d5aa962e/Transroc/images/Exploded_View.png

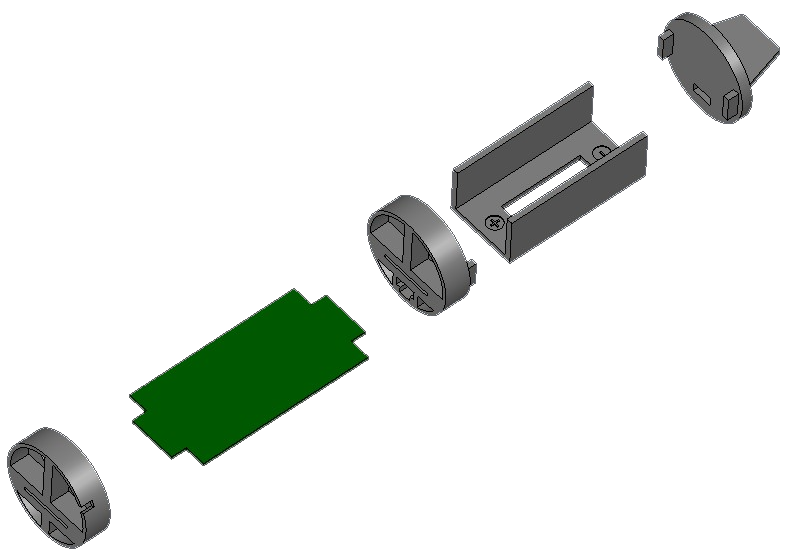
images/Exploded_View.png
