d5aa962e/Transroc/Photos/3D Model.png

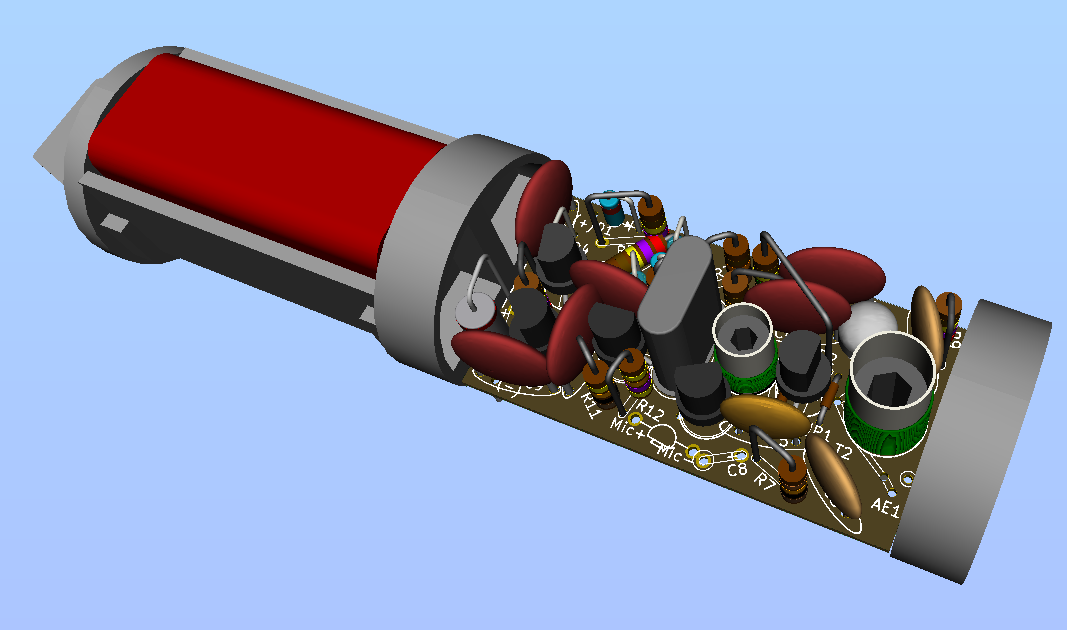
Photos/3D Model.png
