d5aa962e/Transroc/Photos/20210210_202059.jpg

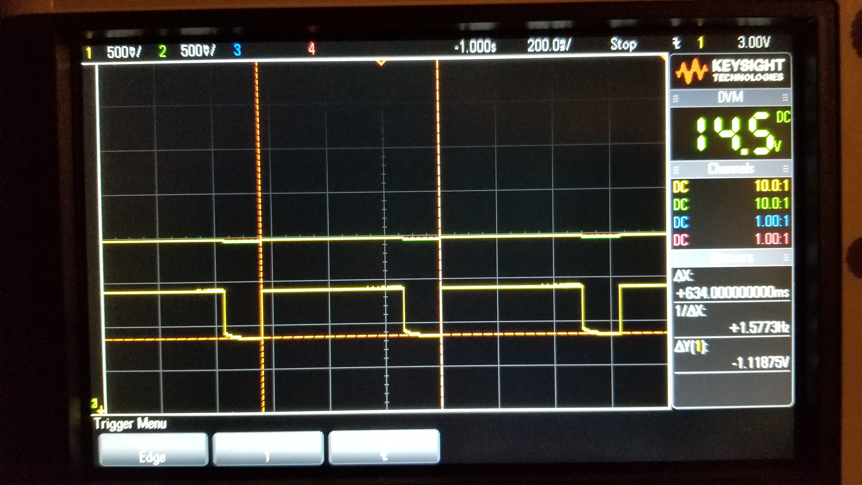
Photos/20210210_202059.jpg
