d5aa962e/Transroc/Photos/20210210_202735.jpg

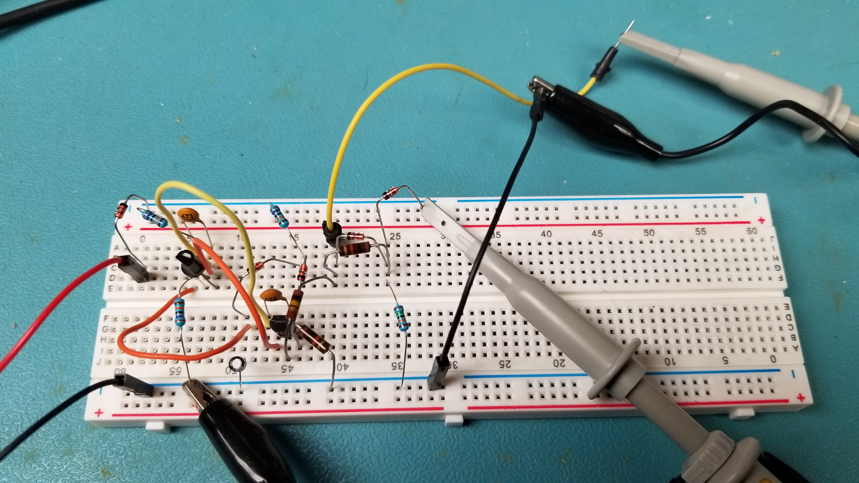
Photos/20210210_202735.jpg
