d5aa962e/Transroc/Photos/20210211_202033.jpg

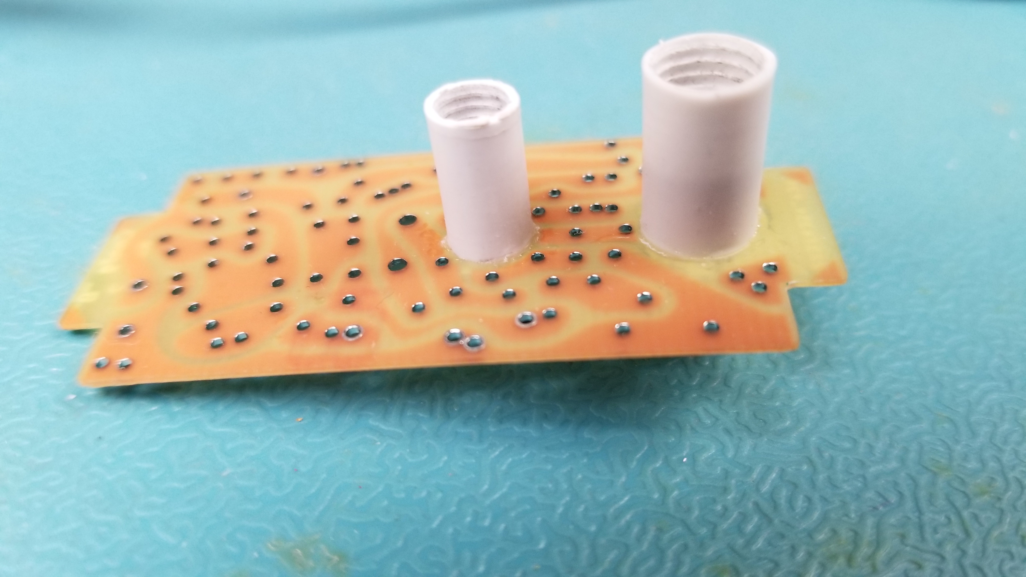
Photos/20210211_202033.jpg
