d5aa962e/Transroc/Photos/20210211_202049.jpg

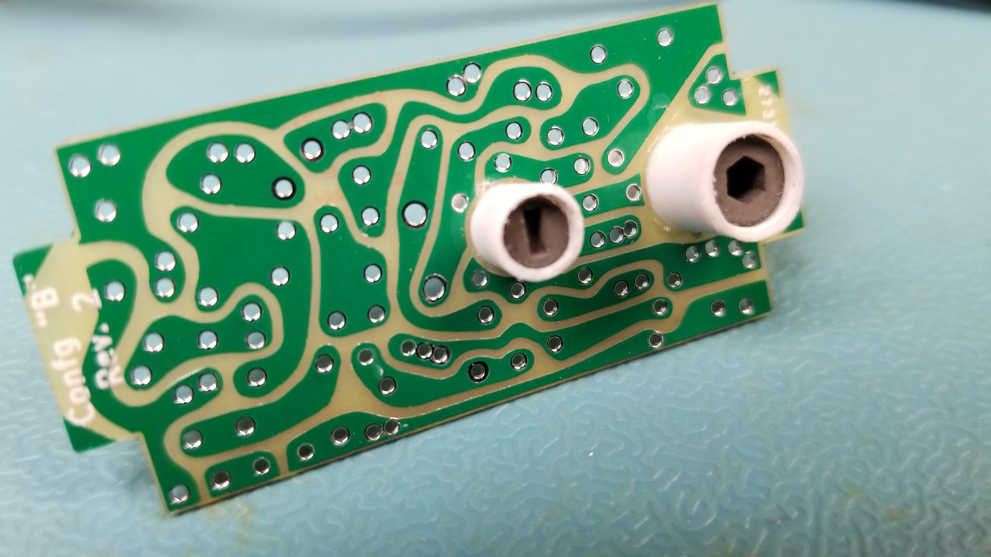
Photos/20210211_202049.jpg
