d5aa962e/Transroc/Photos/20210211_203920.jpg

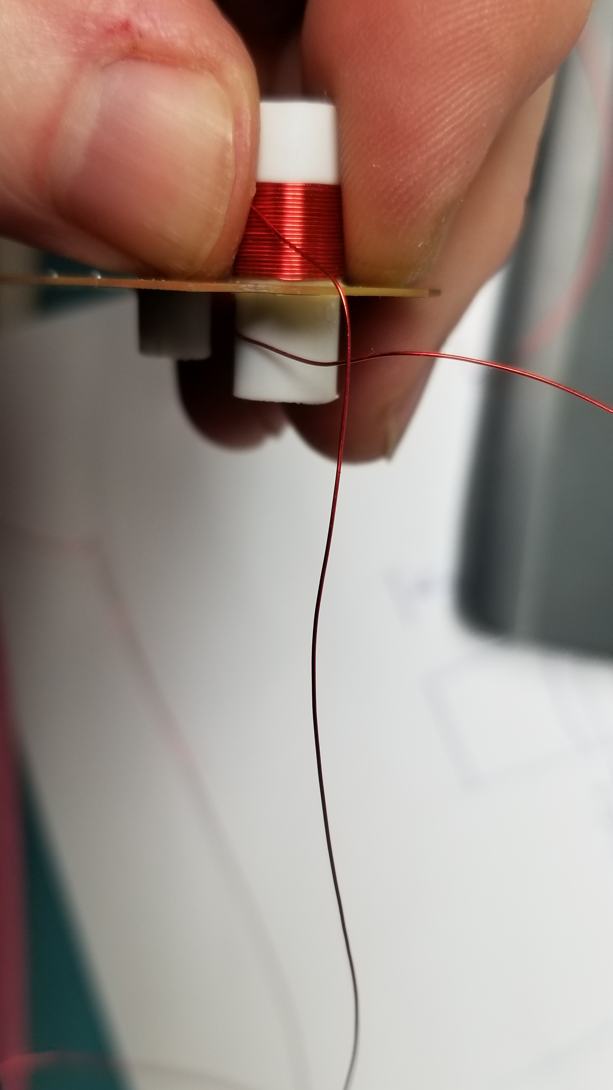
Photos/20210211_203920.jpg
