d5aa962e/Transroc/Photos/20210213_082918.jpg

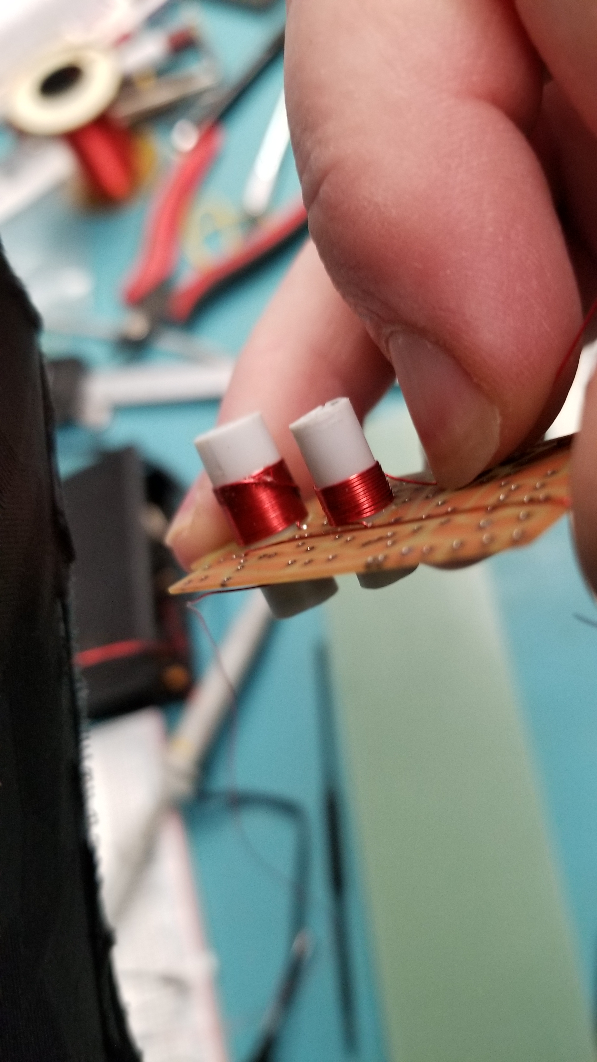
Photos/20210213_082918.jpg
