d5aa962e/Transroc/Photos/20210707_223943.jpg

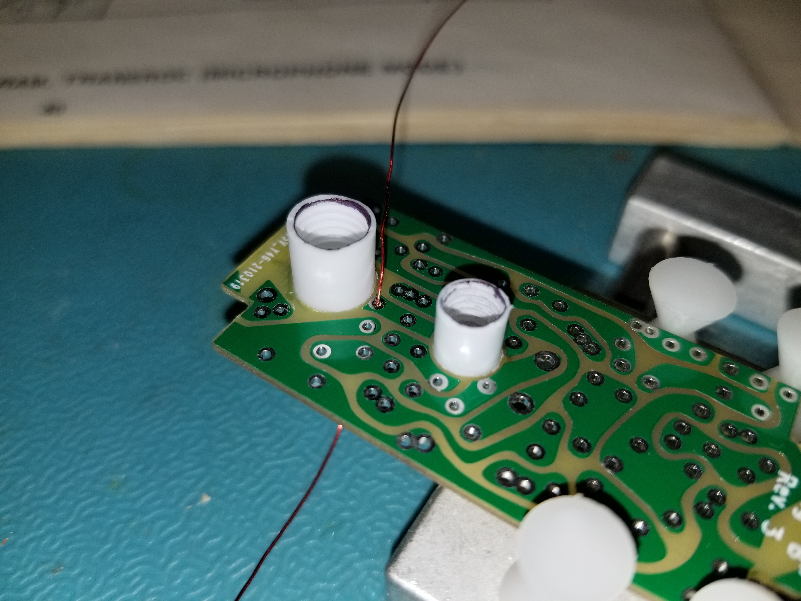
Photos/20210707_223943.jpg
