d5aa962e/Transroc/Photos/20210707_230140.jpg

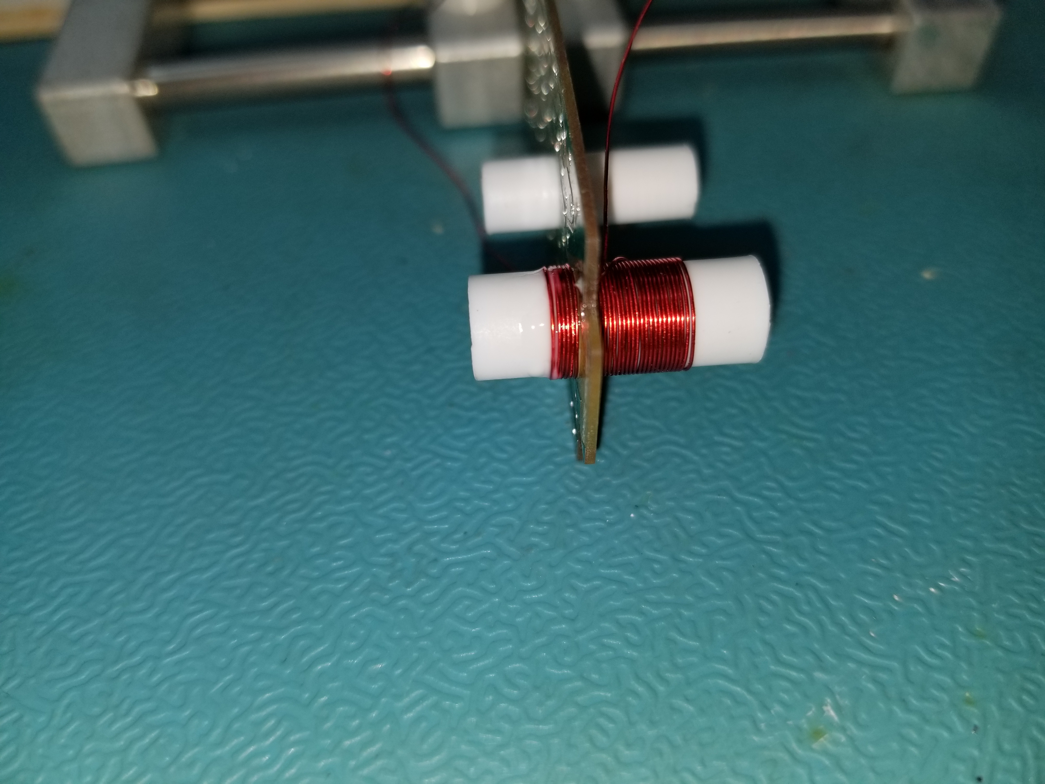
Photos/20210707_230140.jpg
