d5aa962e/Transroc/Photos/20210707_232322.jpg

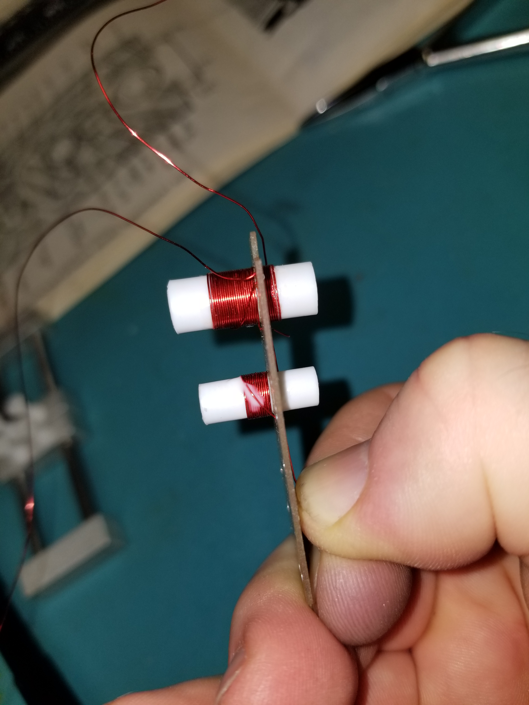
Photos/20210707_232322.jpg
