d5aa962e/Transroc/Photos/20210707_233321.jpg

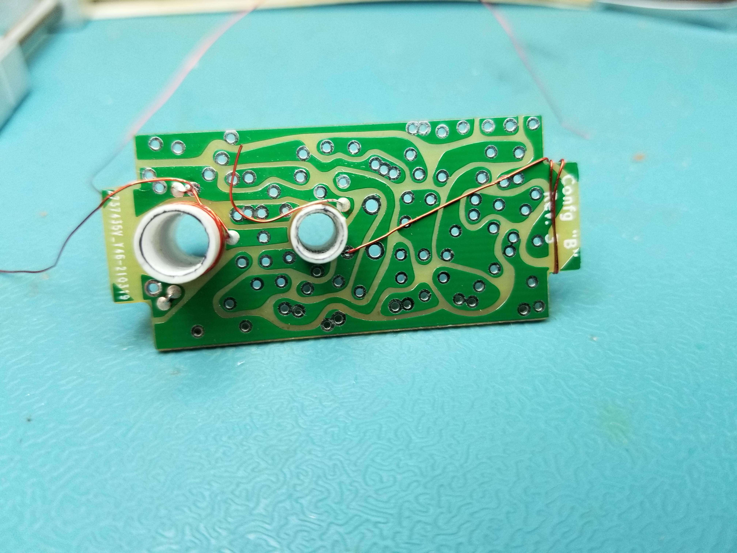
Photos/20210707_233321.jpg
