d5aa962e/Transroc/Photos/20210708_203227.jpg

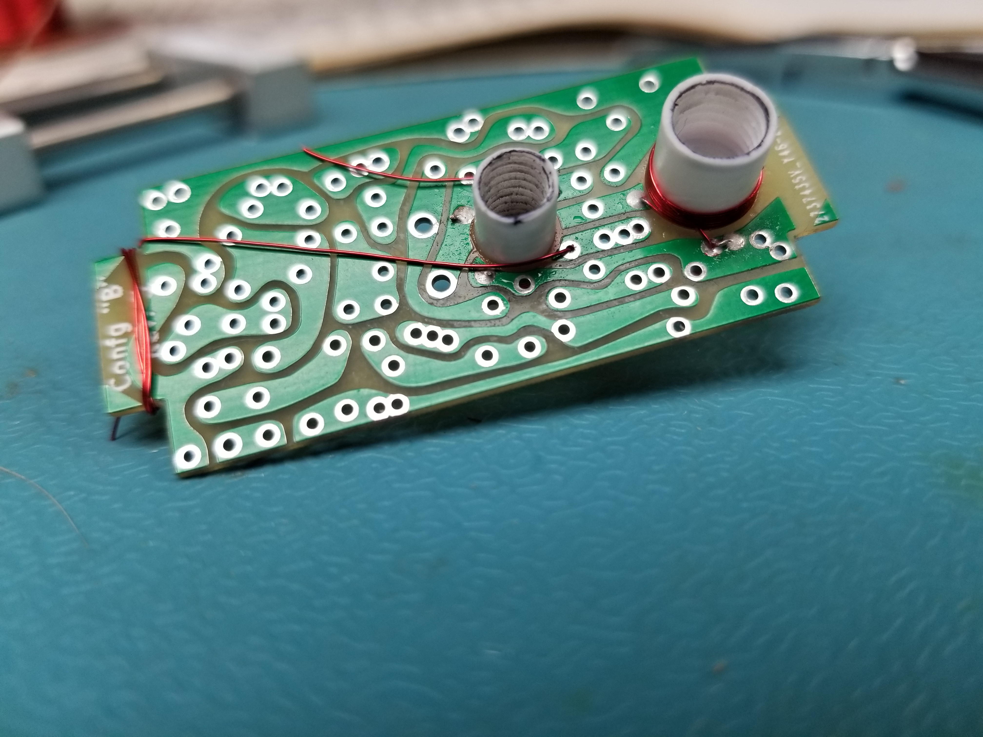
Photos/20210708_203227.jpg
