d5aa962e/Transroc/Photos/20210708_211325.jpg

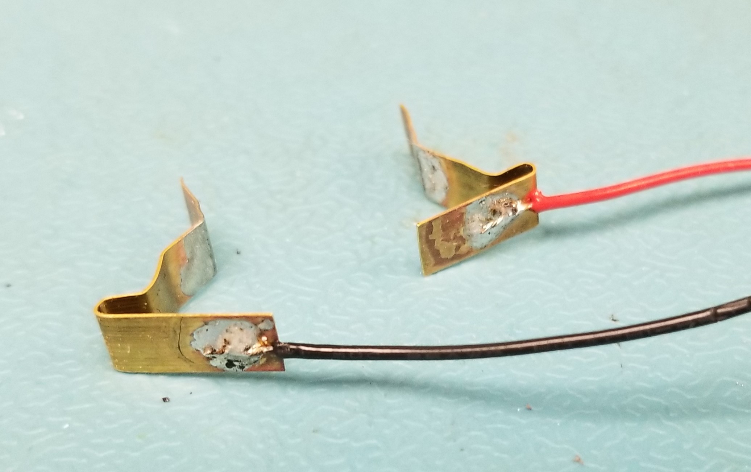
Photos/20210708_211325.jpg
