d5aa962e/Transroc/Photos/20210708_211338.jpg

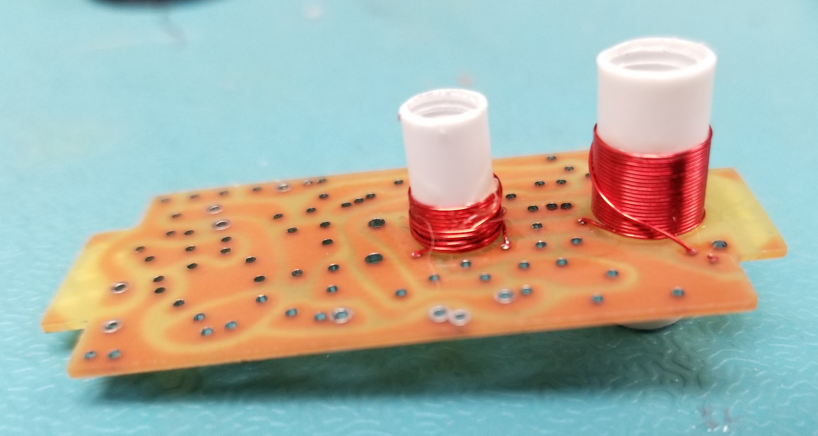
Photos/20210708_211338.jpg
