d5aa962e/Transroc/Photos/20210708_211359.jpg

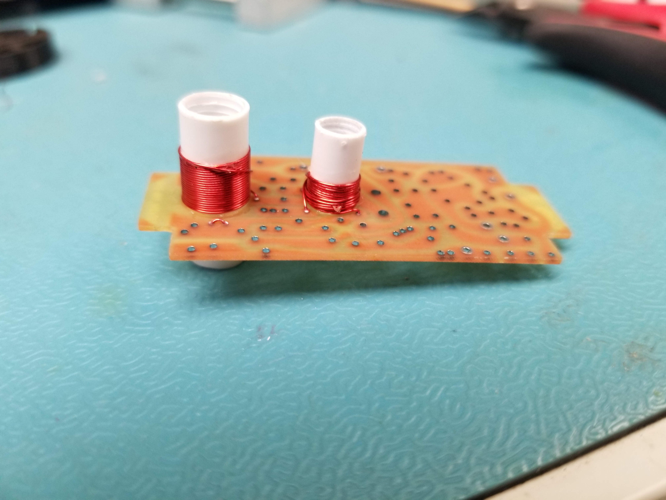
Photos/20210708_211359.jpg
