d5aa962e/Transroc/Photos/20210708_211550.jpg

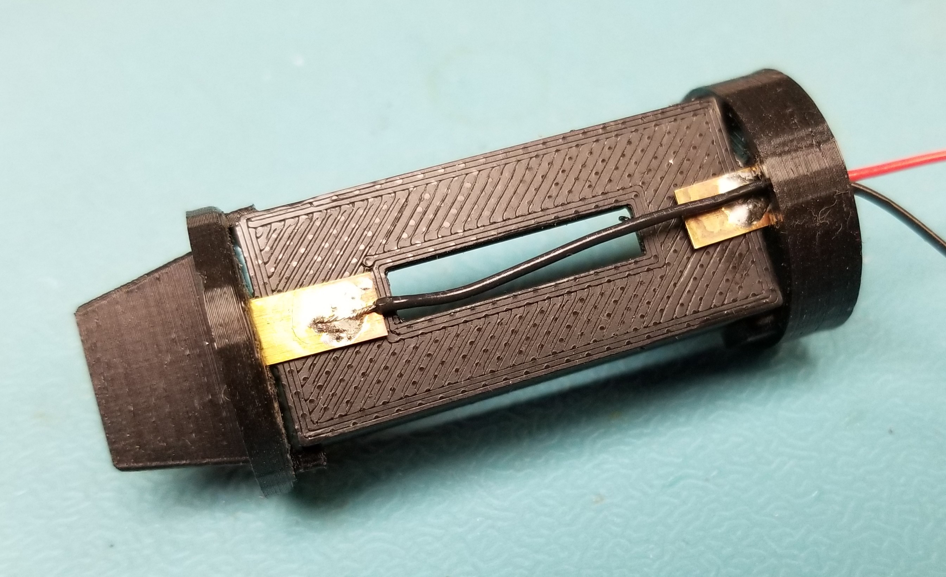
Photos/20210708_211550.jpg
