d5aa962e/Transroc/Photos/20210708_213011.jpg

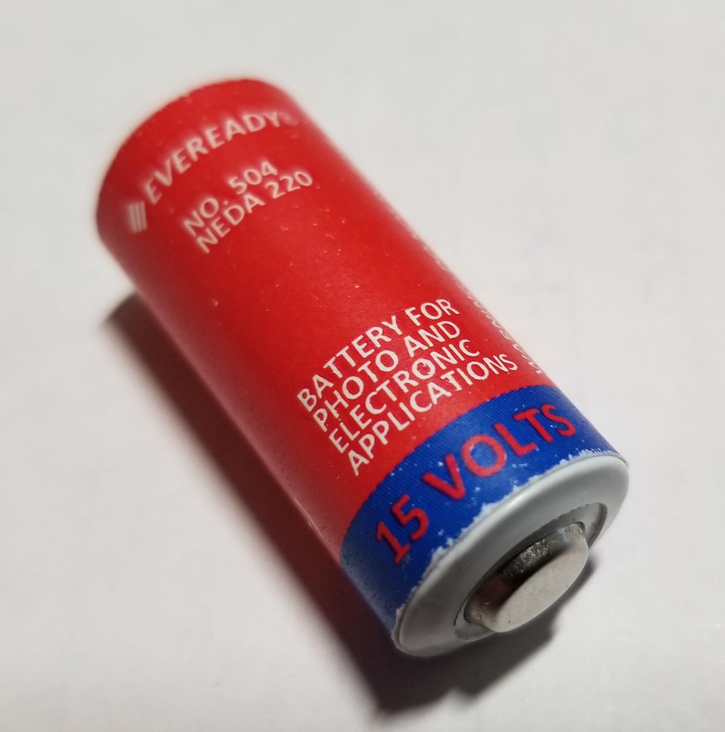
Photos/20210708_213011.jpg
