d5aa962e/Transroc/Photos/20210708_214236-a.jpg

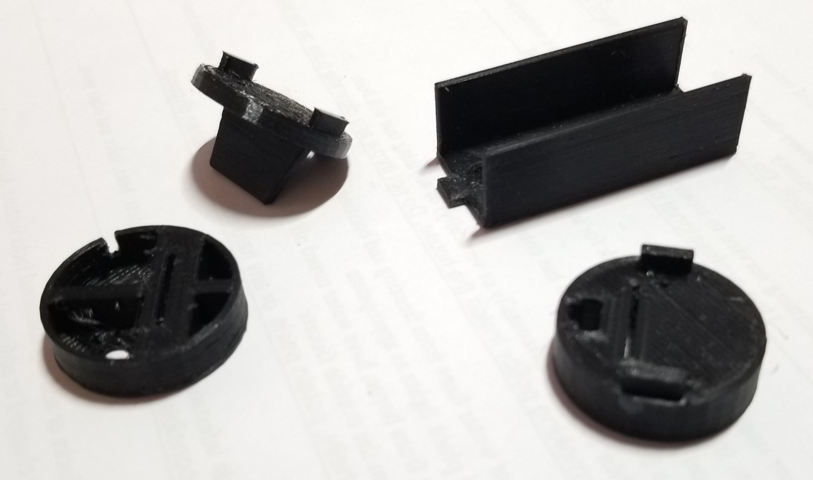
Photos/20210708_214236-a.jpg
