d5aa962e/Transroc/Photos/20210826_221735a.jpg

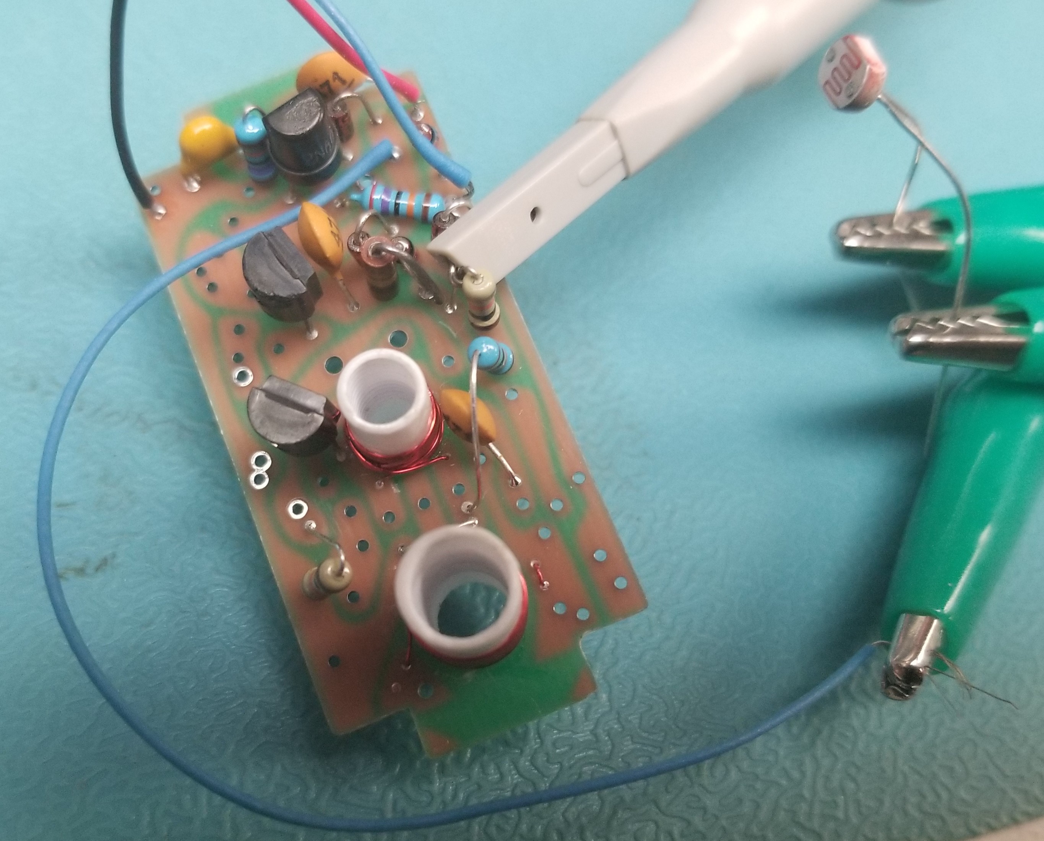
Photos/20210826_221735a.jpg
