d5aa962e/Transroc/Photos/20210826_221752.jpg

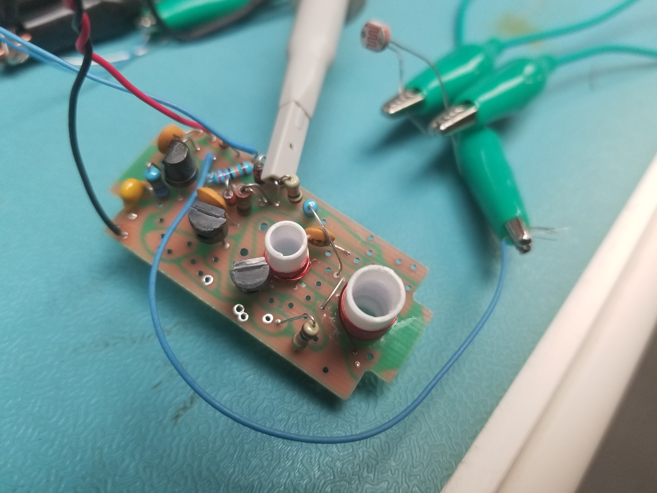
Photos/20210826_221752.jpg
