d5aa962e/Transroc/Photos/20210830_192405.jpg

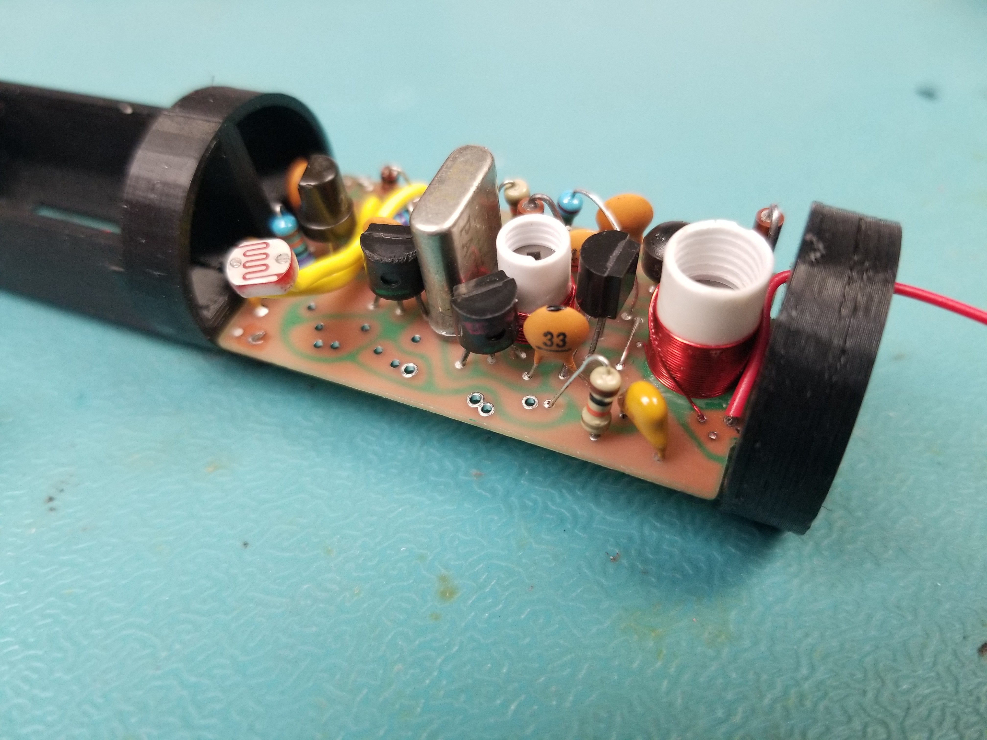
Photos/20210830_192405.jpg
