d5aa962e/Transroc/Photos/20210830_200806.jpg

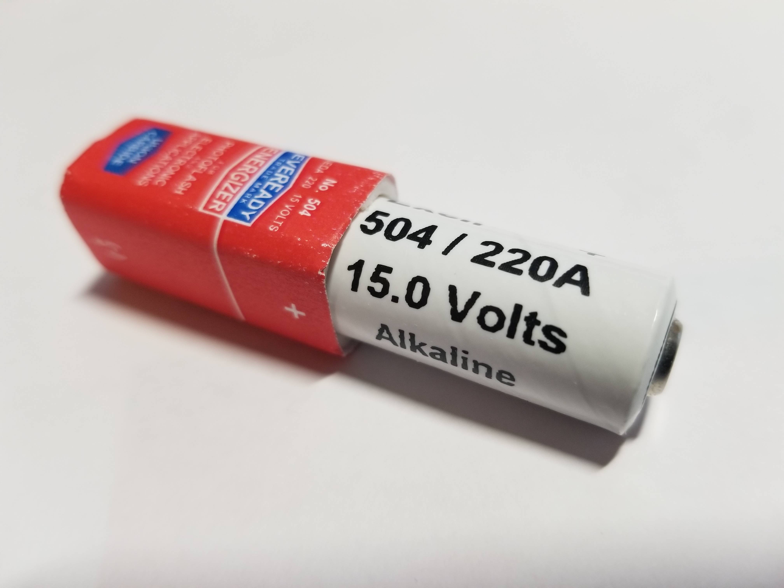
Photos/20210830_200806.jpg
