d5aa962e/Transroc/Photos/20210830_201057.jpg

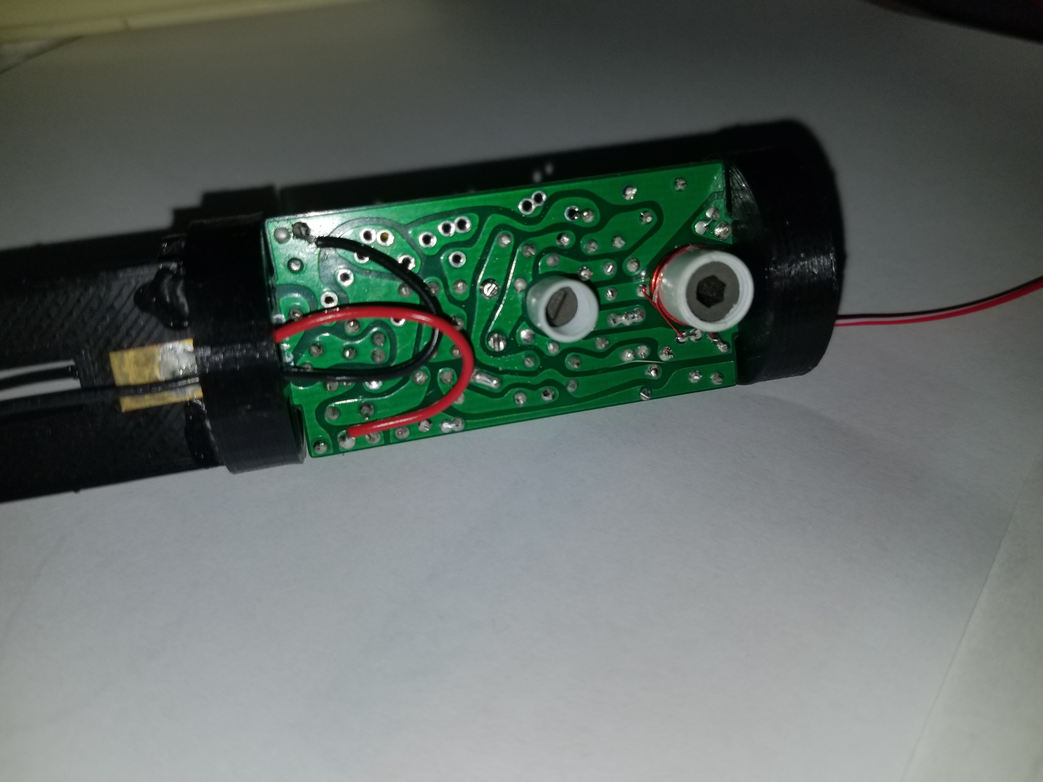
Photos/20210830_201057.jpg
