d5aa962e/Transroc/Photos/20210830_201219.jpg

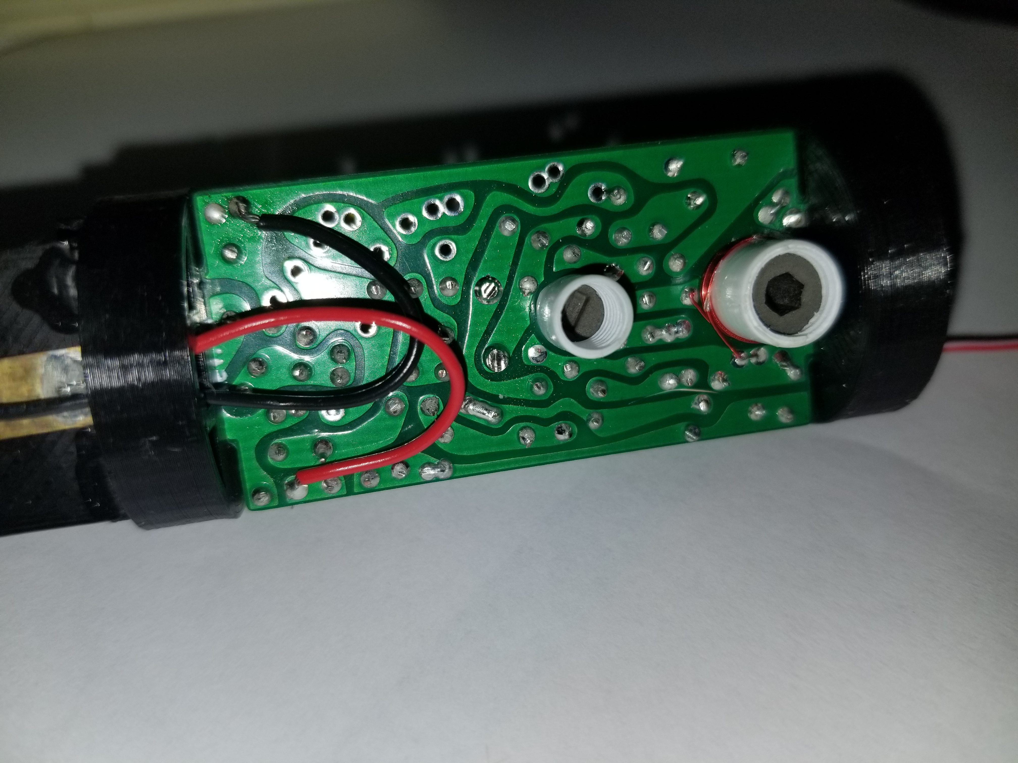
Photos/20210830_201219.jpg
