d5aa962e/Transroc/Photos/20210830_201253.jpg

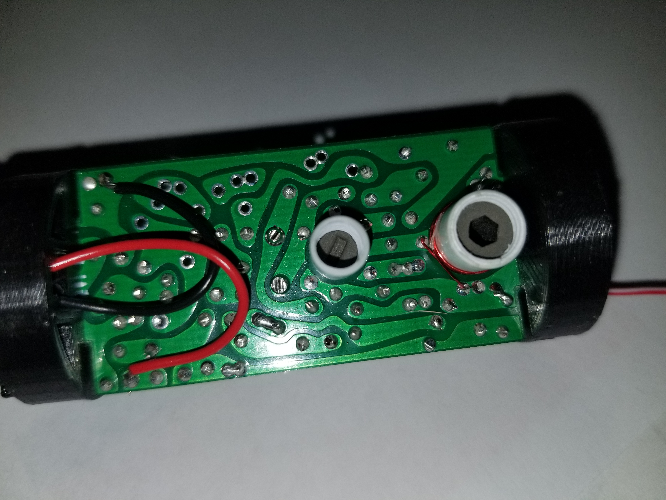
Photos/20210830_201253.jpg
