d5aa962e/Transroc/Photos/20210830_201328.jpg

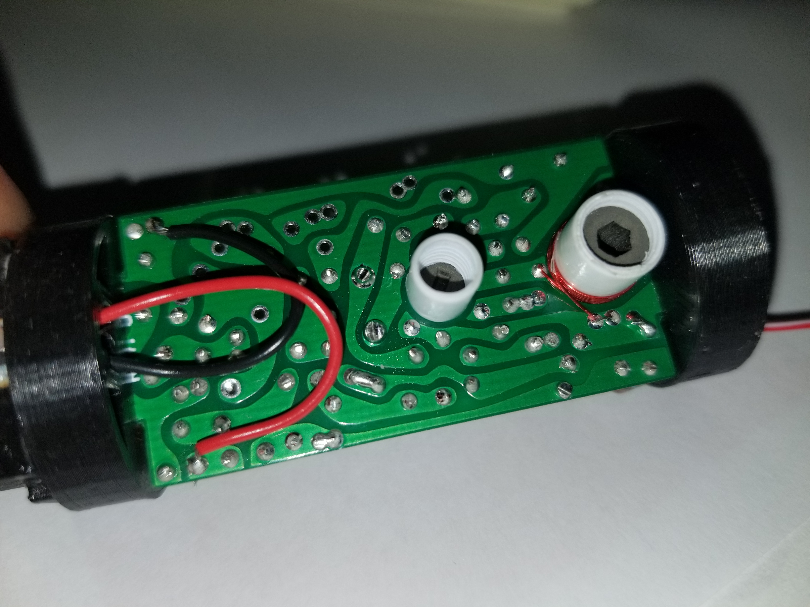
Photos/20210830_201328.jpg
