d5aa962e/Transroc/Photos/Blank Boards.jpg

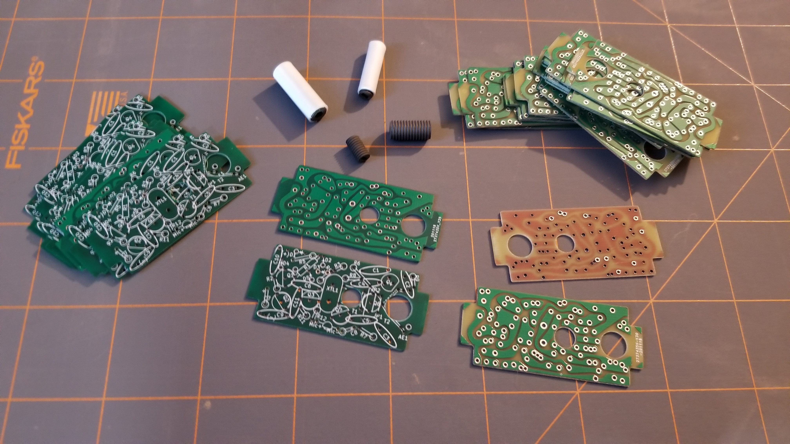
Photos/Blank Boards.jpg
