d5aa962e/Transroc/Photos/RocketGuy101_Models/P5262098MR.jpg

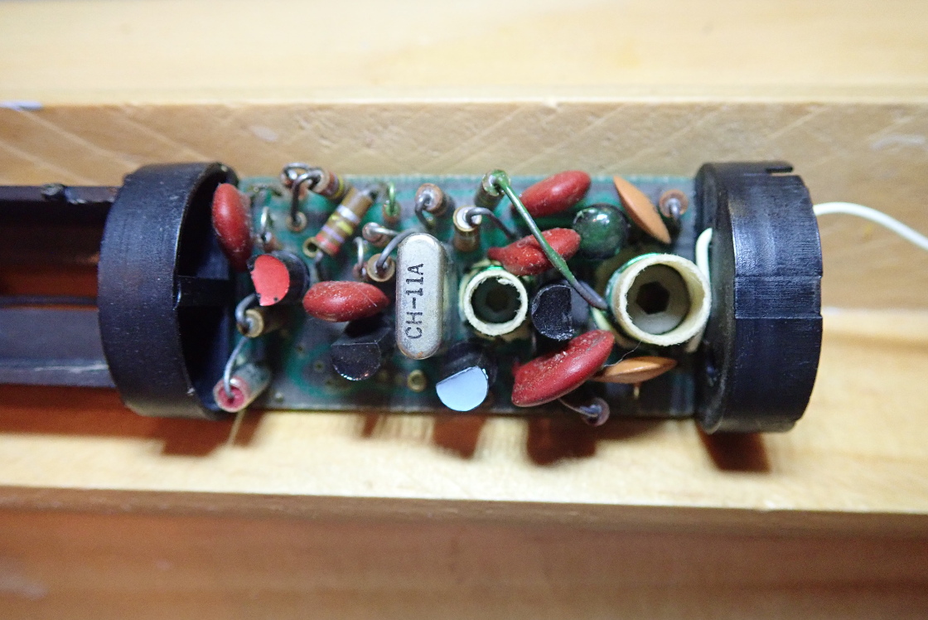
Photos/RocketGuy101_Models/P5262098MR.jpg
