d5aa962e/Transroc/Photos/RocketGuy101_Models/P6262291.jpg

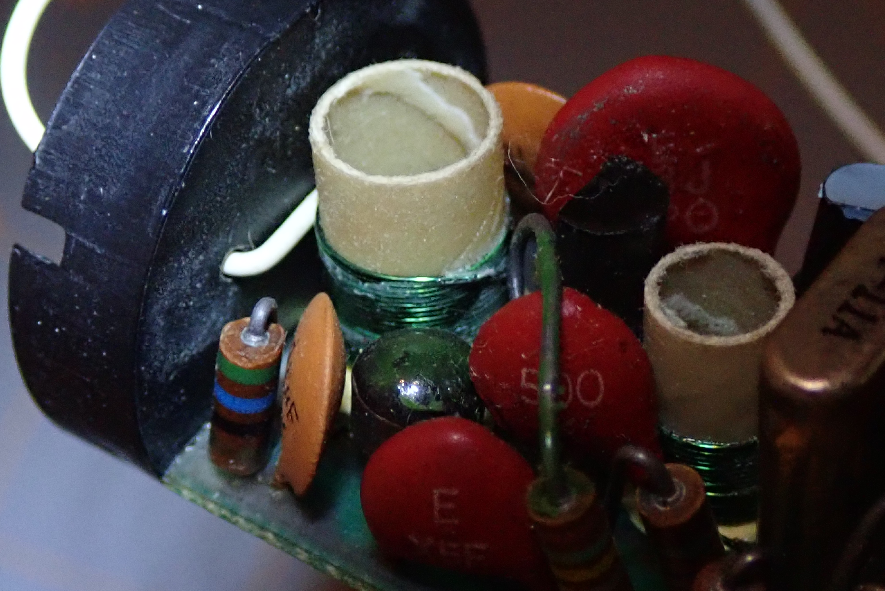
Photos/RocketGuy101_Models/P6262291.jpg
