d5aa962e/Transroc/Photos/RocketGuy101_Models/P6262298.jpg

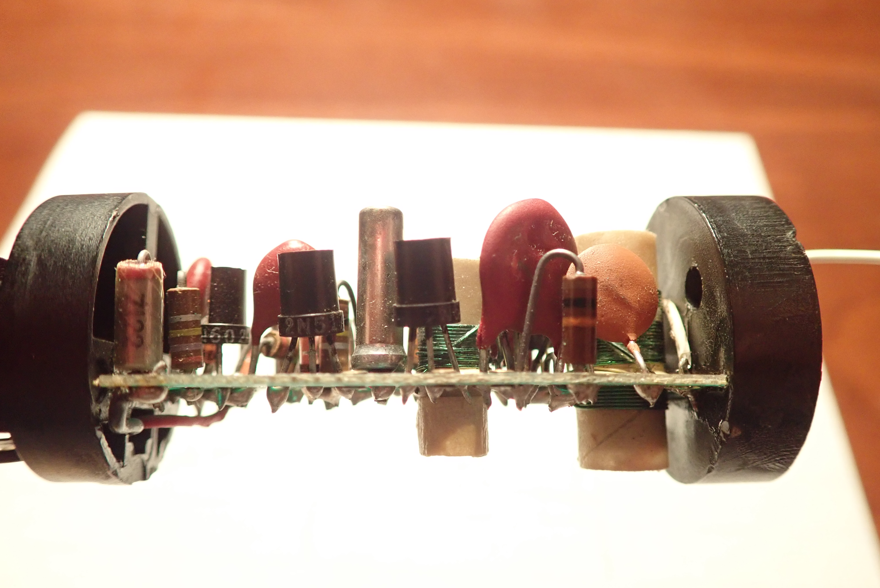
Photos/RocketGuy101_Models/P6262298.jpg
