d5aa962e/Transroc/Photos/RocketGuy101_Models/P6262299.jpg

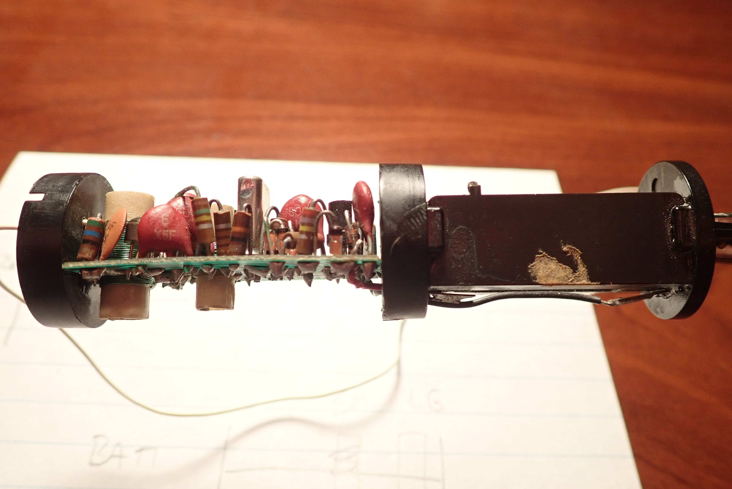
Photos/RocketGuy101_Models/P6262299.jpg
