d5aa962e/Transroc/Photos/RocketGuy101_Models/P6262300.jpg

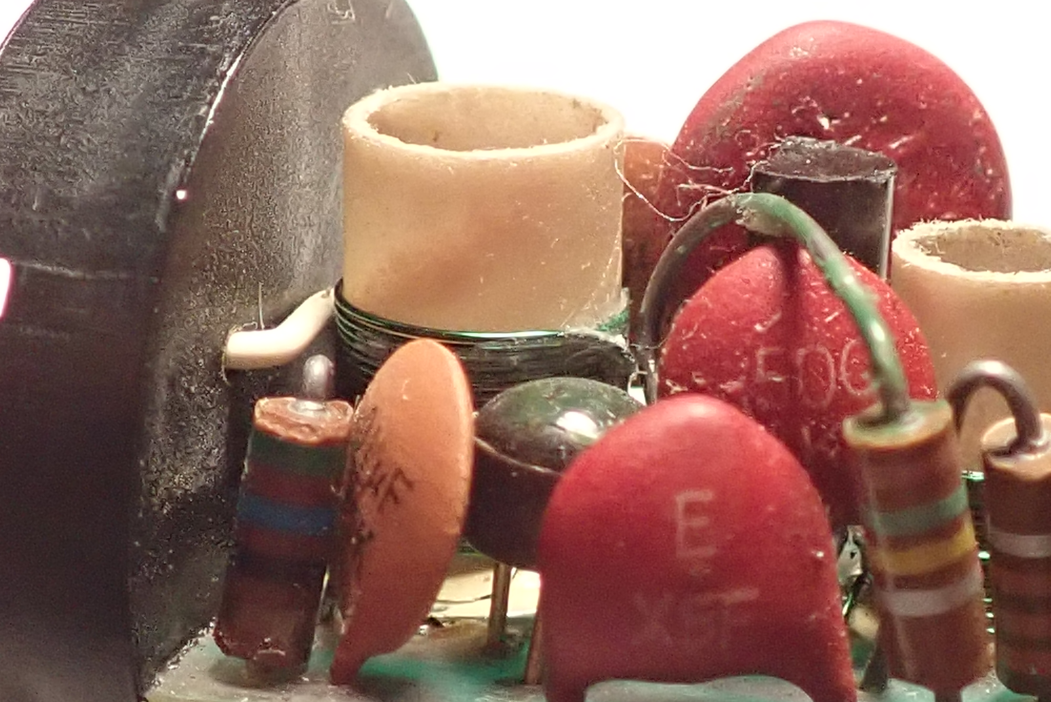
Photos/RocketGuy101_Models/P6262300.jpg
