d5aa962e/Transroc/Photos/RocketGuy101_Models/P6262301.jpg

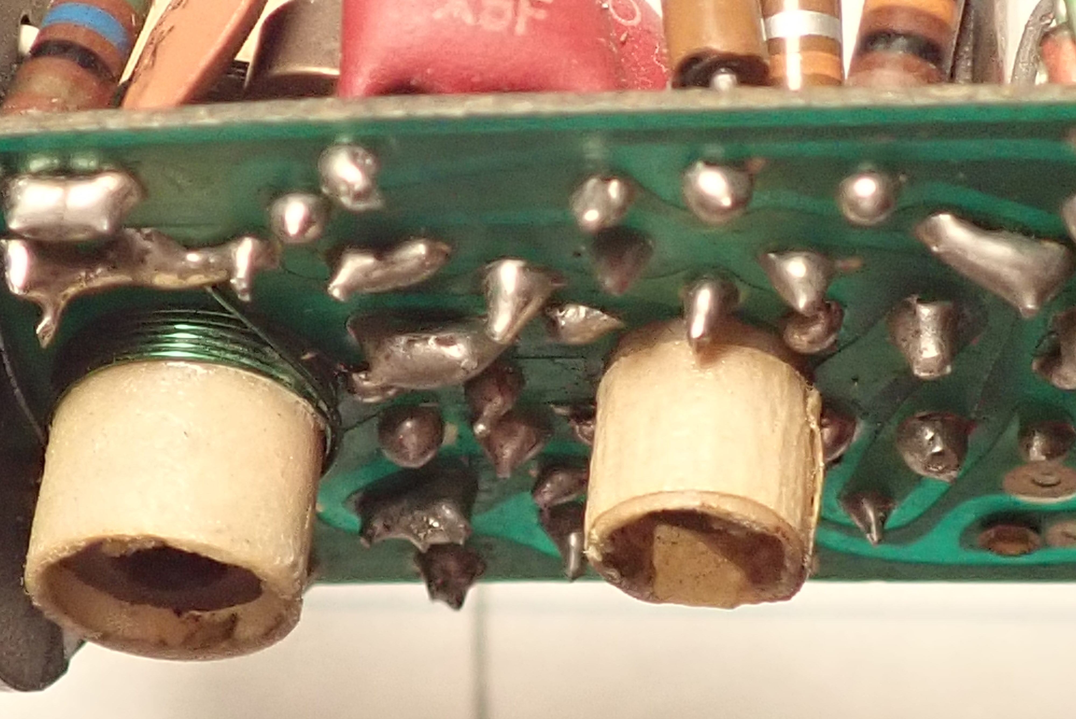
Photos/RocketGuy101_Models/P6262301.jpg
