d5aa962e/Transroc/Photos/RocketGuy101_Models/TransrocAssy.jpg

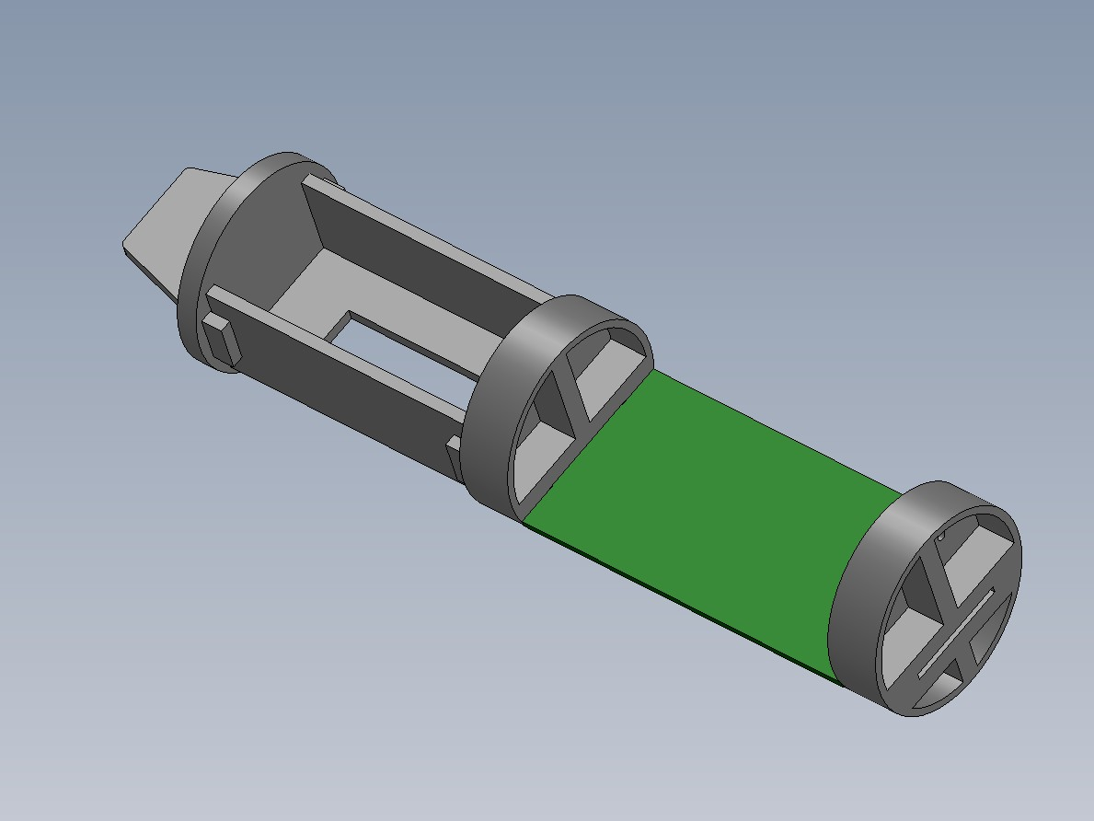
Photos/RocketGuy101_Models/TransrocAssy.jpg
