d5aa962e/Transroc/Photos/RocketGuy101_Models/TransrocAssyExp.jpg

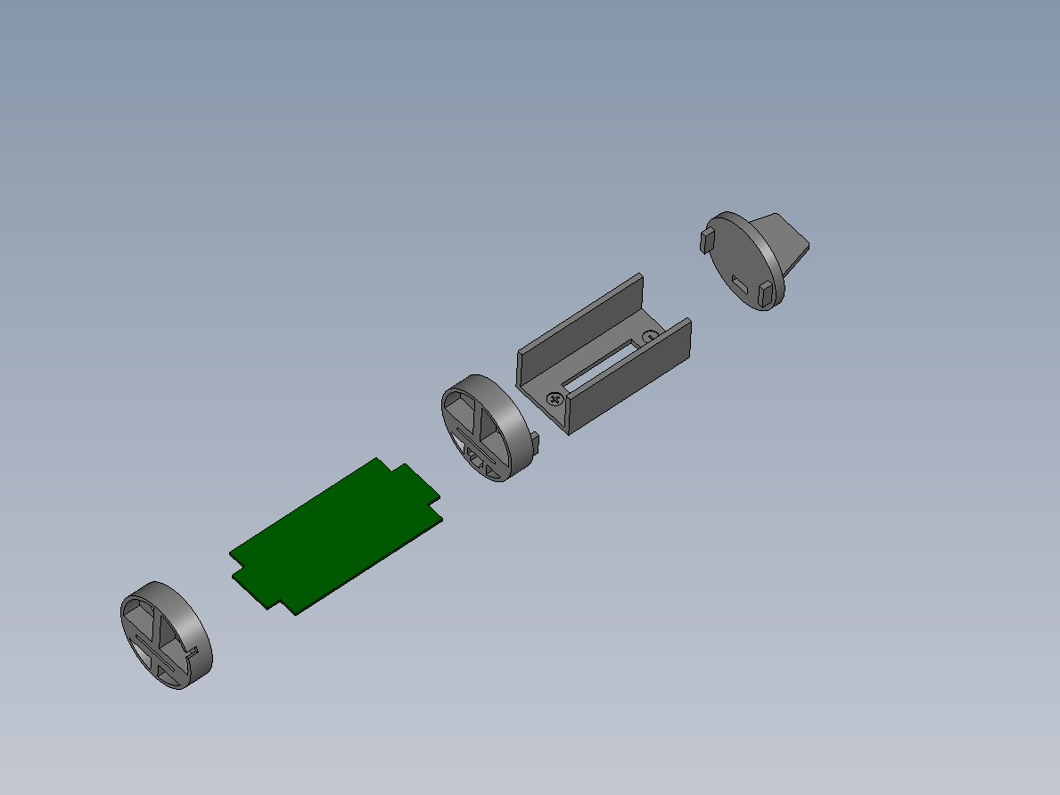
Photos/RocketGuy101_Models/TransrocAssyExp.jpg
