d5aa962e/Transroc/Photos/Screenshot 2021-08-26 214938.png

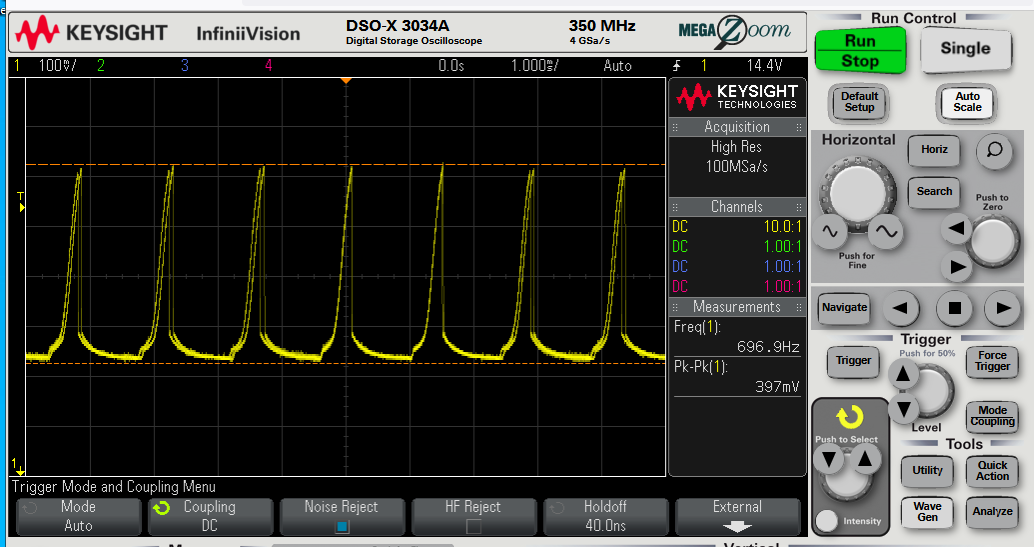
Photos/Screenshot 2021-08-26 214938.png
