d5aa962e/Transroc/Photos/Transroc-0001.jpg

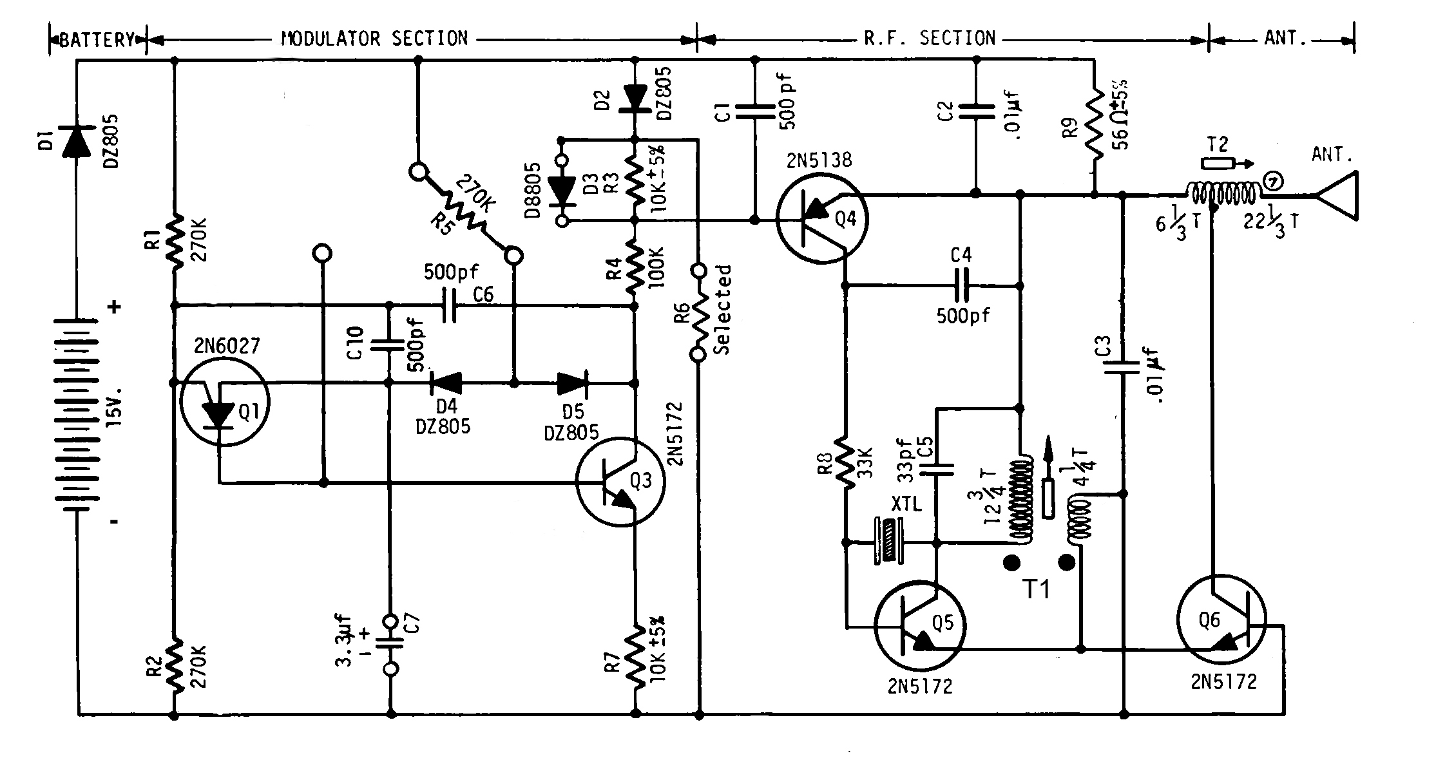
Photos/Transroc-0001.jpg
