d5aa962e/Transroc/Component_Models/Resistor Model.FCStd

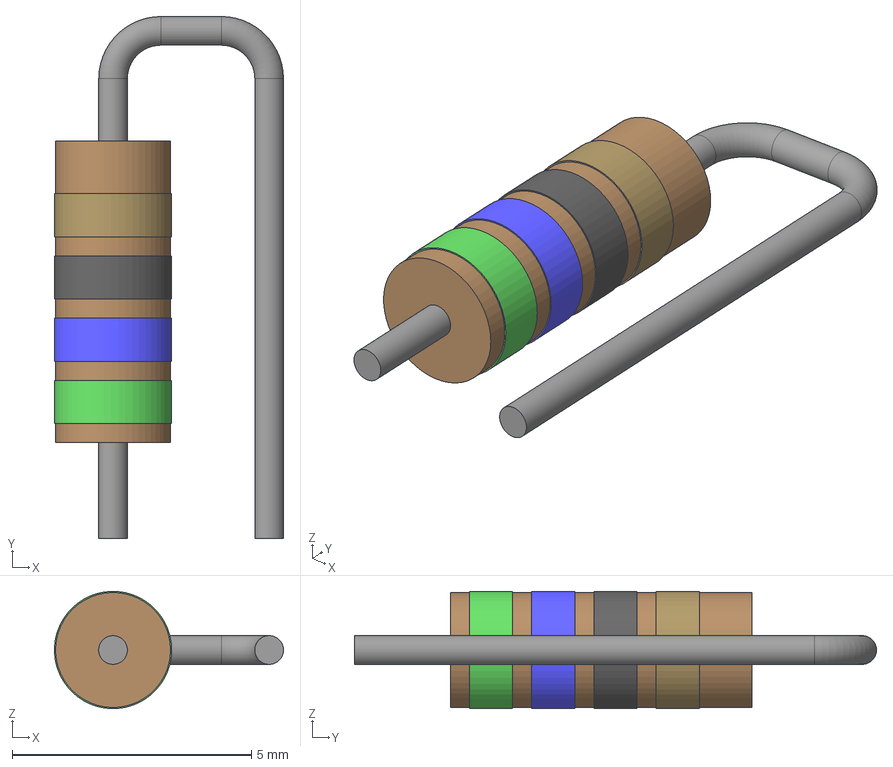
[picture p83: CAD file, 2021-09-29]
Component_Models/Resistor Model.FCStd
4.78 x 10.9 x 2.45 mm
Body-Band2
Body-Band1
Body-Band3
Body-Band4
