d5aa962e/Transroc/Component_Models/Cap-Elect.FCStd

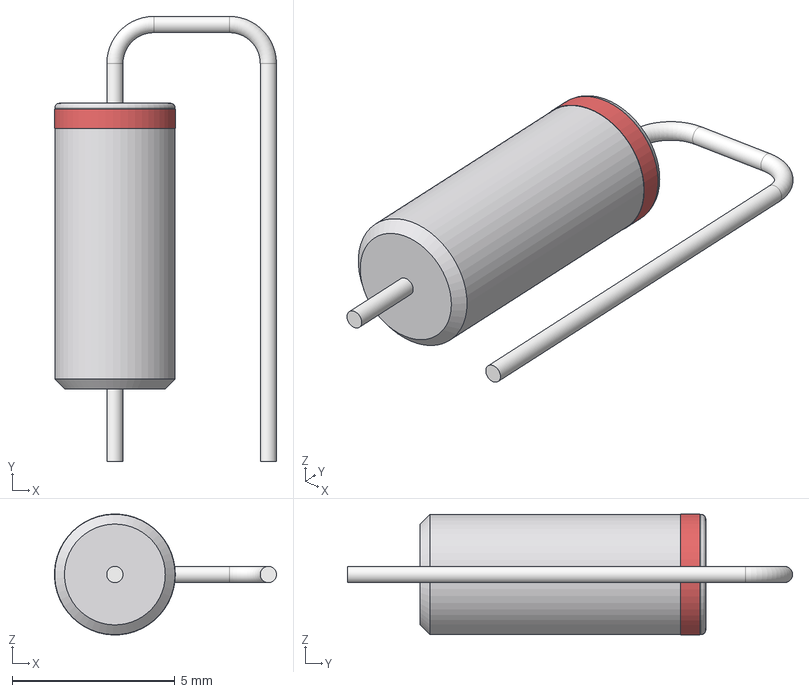
[picture p84: CAD file, 2021-09-29]
Component_Models/Cap-Elect.FCStd
6.83 x 13.7 x 3.72 mm
