d5aa962e/Transroc/Component_Models/Battery Carrier-A23.FCStd

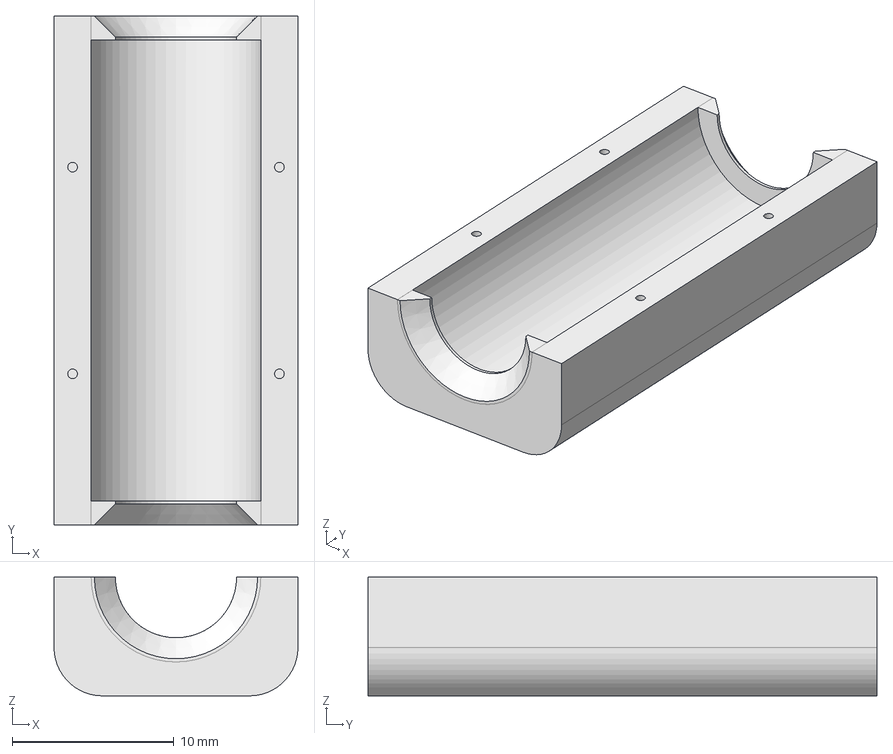
[picture p85: CAD file, 2021-09-29]
Component_Models/Battery Carrier-A23.FCStd
15.1 x 31.5 x 7.35 mm
