d5aa962e/Transroc/STL Files/Battery_Carrier-504-Half.stl

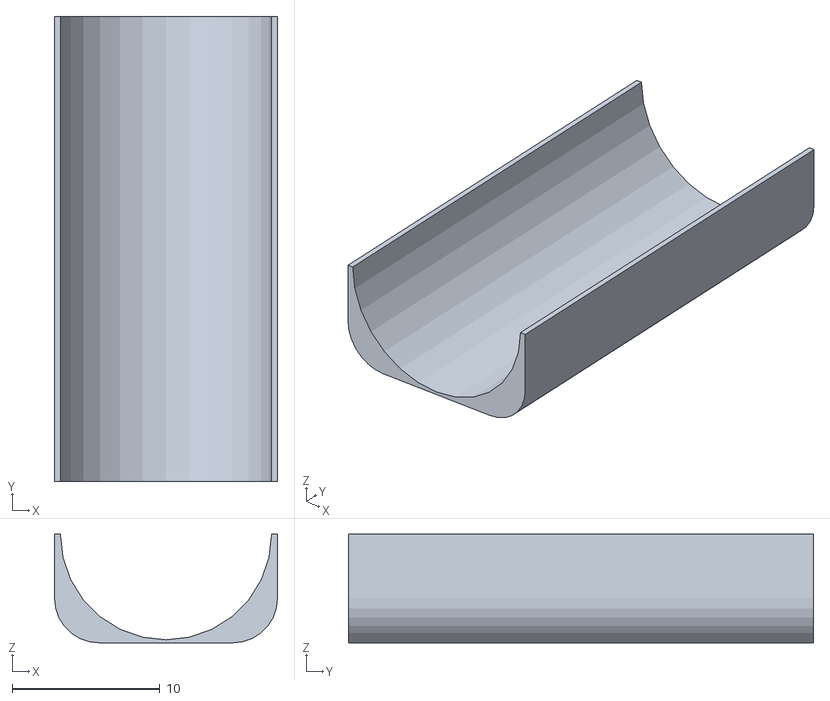
[picture p86: CAD file, 2021-09-29]
STL Files/Battery_Carrier-504-Half.stl
15.1 x 31.5 x 7.35
