d5aa962e/Transroc/Component_Models/Bottom_Mount_2.FCStd

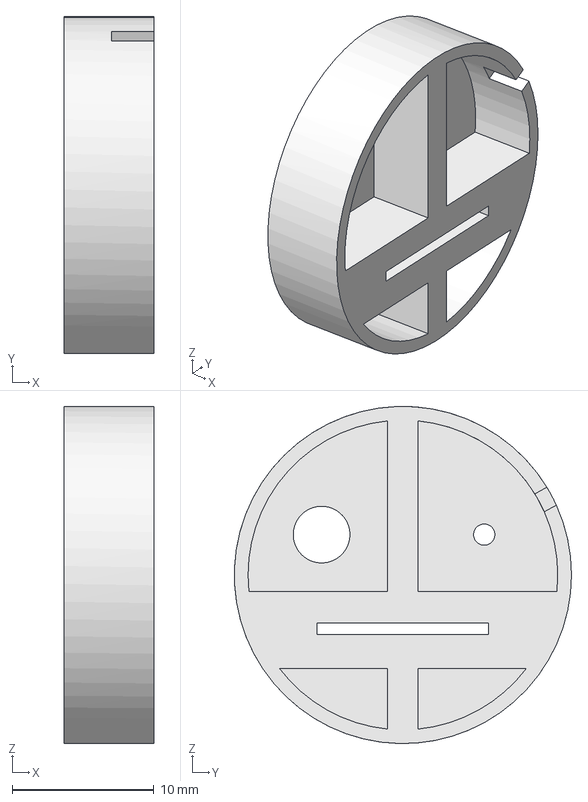
[picture p87: CAD file, 2021-09-29]
Component_Models/Bottom_Mount_2.FCStd
6.35 x 23.8 x 23.8 mm
