d5aa962e/Transroc/Component_Models/Jumper-Short.FCStd

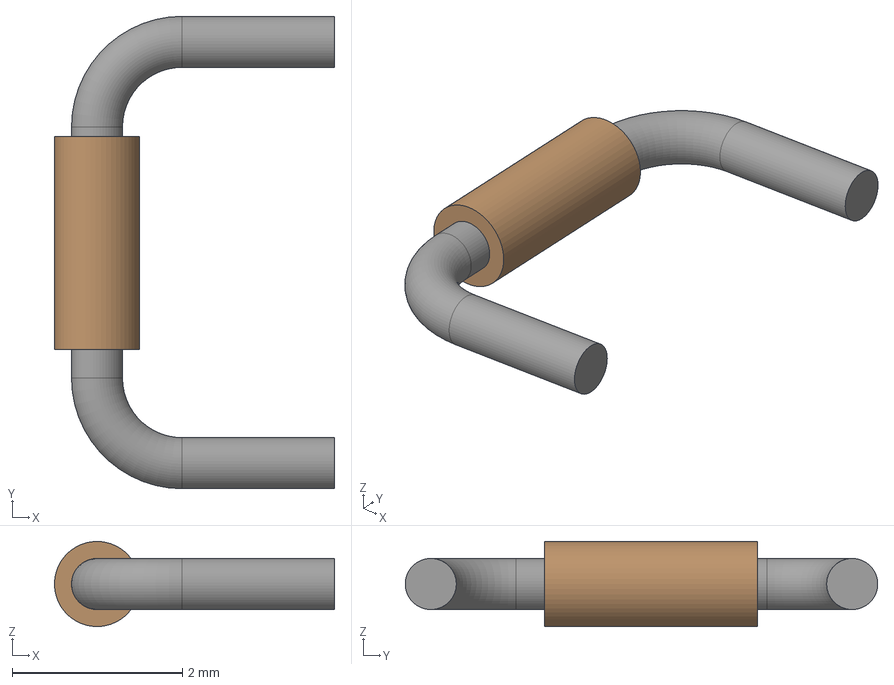
[picture p88: CAD file, 2021-09-29]
Component_Models/Jumper-Short.FCStd
3.29 x 5.55 x 1 mm
