d5aa962e/Transroc/Component_Models/Cap-Disk-7.5mm.FCStd

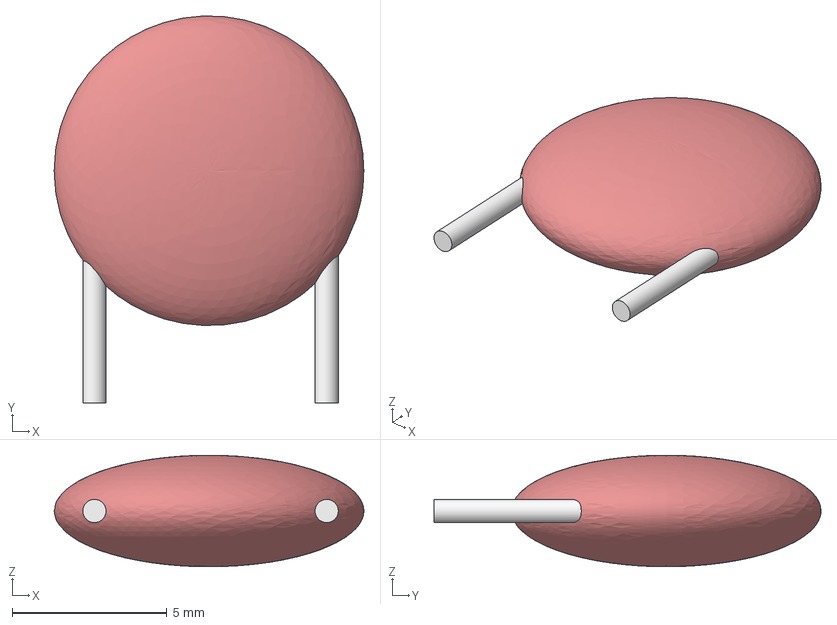
[picture p89: CAD file, 2021-09-29]
Component_Models/Cap-Disk-7.5mm.FCStd
10.00 x 12.5 x 3.60 mm
