d5aa962e/Transroc/Component_Models/TO-106.FCStd

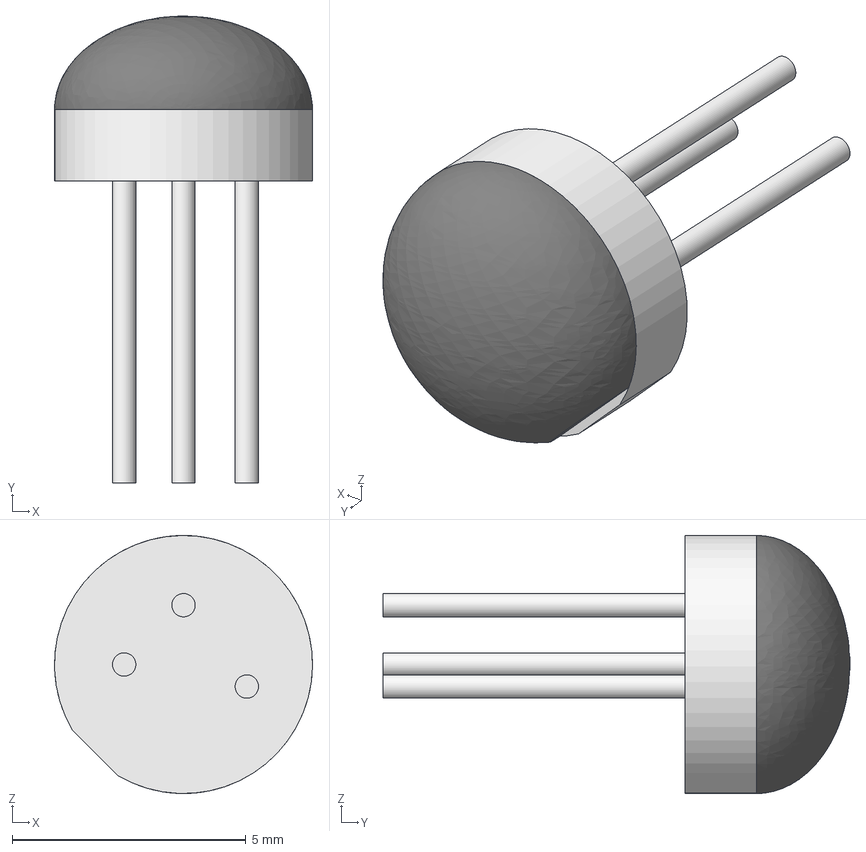
[picture p90: CAD file, 2021-09-29]
Component_Models/TO-106.FCStd
5.53 x 10.00 x 5.53 mm
Tophat
Pin1
PIn2
Pin3
