d5aa962e/Transroc/Component_Models/TO-98.FCStd

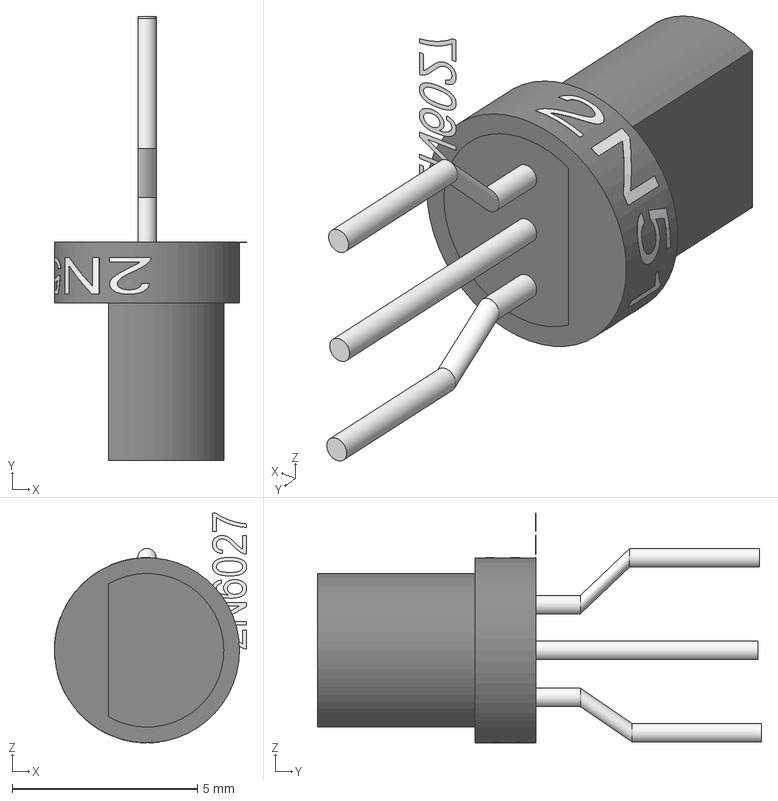
[picture p91: CAD file, 2021-09-29]
Component_Models/TO-98.FCStd
5.20 x 12.0 x 6.21 mm
Rim
MainBody
CenterPin
ShapeString
Sketch_On_Surface
