d5aa962e/Transroc/Component_Models/Antenna Coil.FCStd

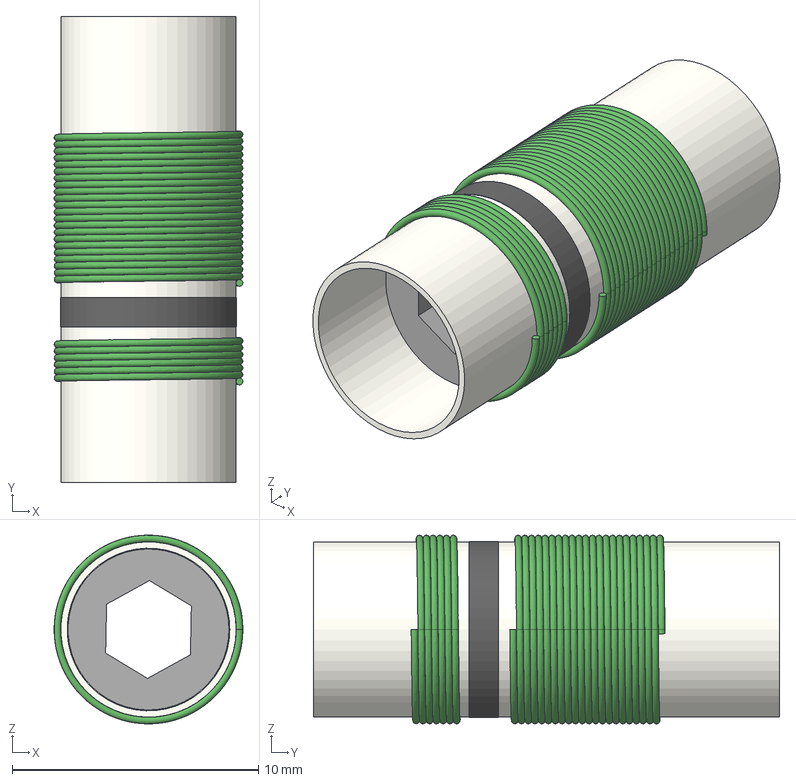
[picture p92: CAD file, 2021-09-29]
Component_Models/Antenna Coil.FCStd
7.66 x 18.9 x 7.66 mm
Coil Form
Board Band
Coil A
Coil B
Slug Core
