d5aa962e/Transroc/Component_Models/Cap-Disk-5.3mm.FCStd

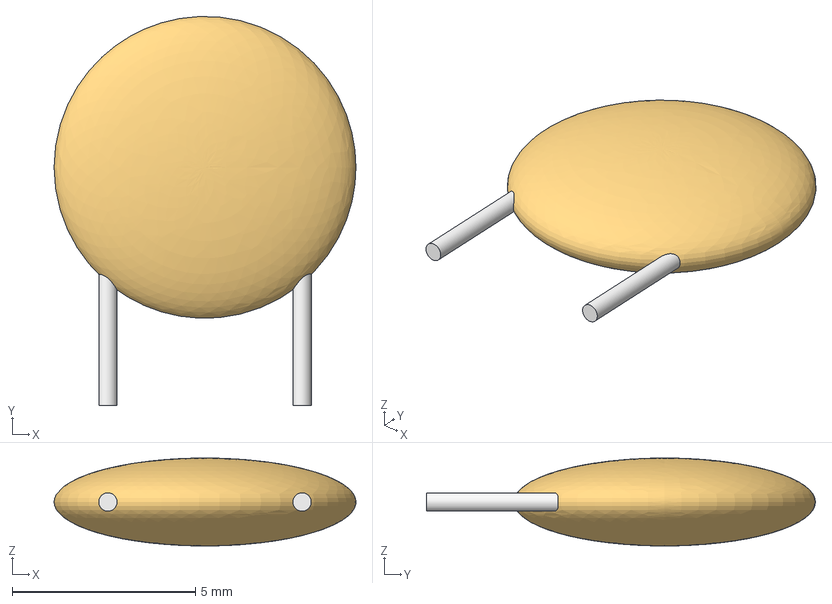
[picture p93: CAD file, 2021-09-29]
Component_Models/Cap-Disk-5.3mm.FCStd
8.24 x 10.6 x 2.40 mm
EllipsoidBody
