d5aa962e/Transroc/Component_Models/Spring_Clip2.FCStd

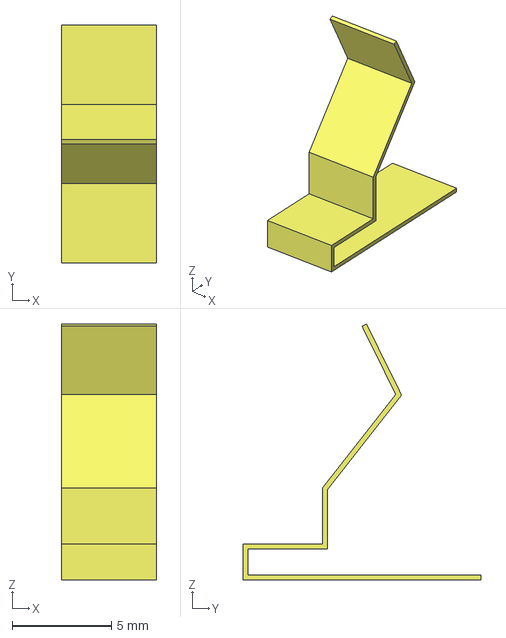
[picture p94: CAD file, 2021-09-29]
Component_Models/Spring_Clip2.FCStd
4.80 x 12.0 x 12.9 mm
