d5aa962e/Transroc/Component_Models/Battery Carrier-504.FCStd

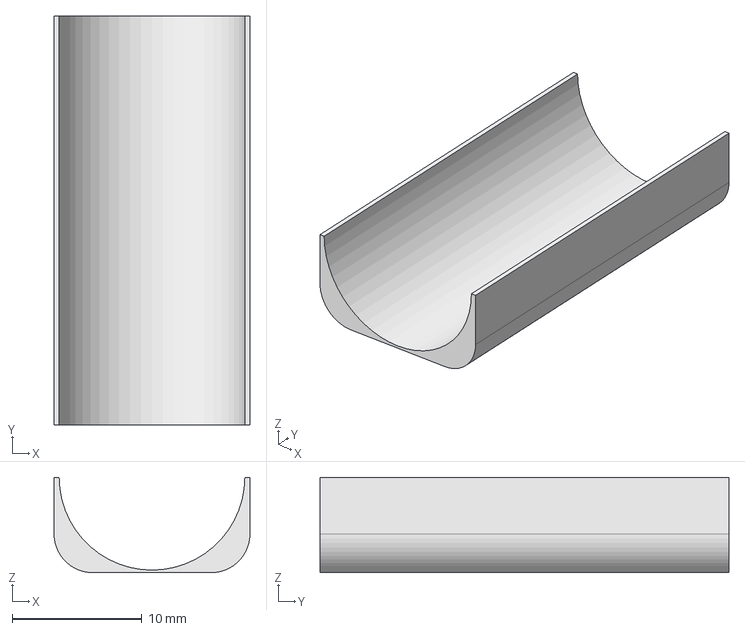
[picture p95: CAD file, 2021-09-29]
Component_Models/Battery Carrier-504.FCStd
15.1 x 31.5 x 7.35 mm
