d5aa962e/Transroc/Component_Models/Cap-Disk-7.5mm-a.FCStd

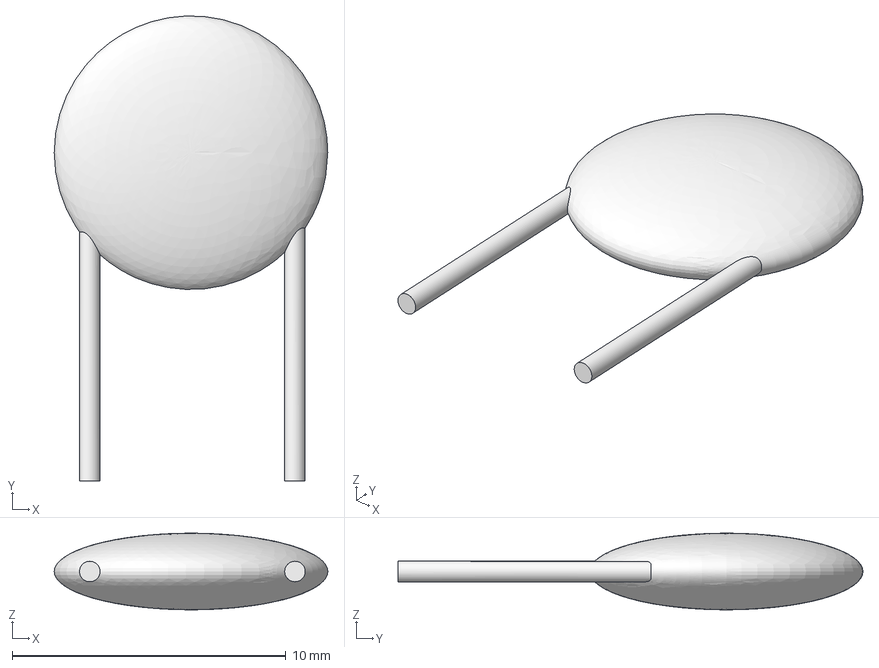
[picture p96: CAD file, 2021-09-29]
Component_Models/Cap-Disk-7.5mm-a.FCStd
10.00 x 17.0 x 2.80 mm
