d5aa962e/Transroc/Component_Models/Cap-Disk-4.5mm.FCStd

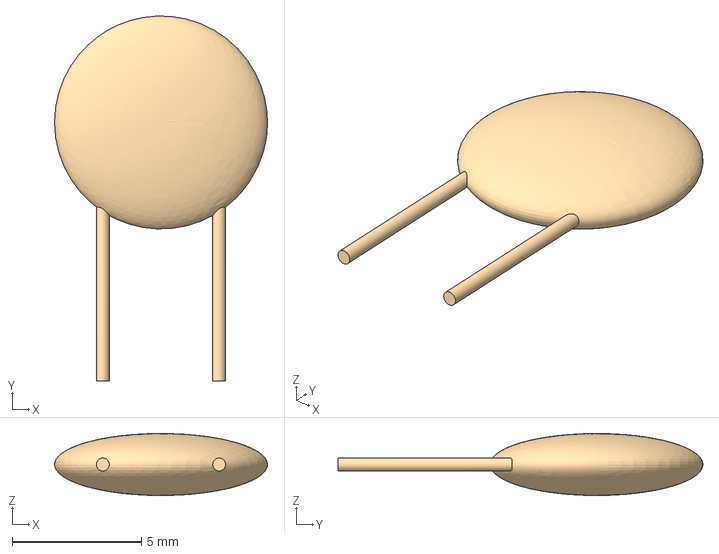
[picture p97: CAD file, 2021-09-29]
Component_Models/Cap-Disk-4.5mm.FCStd
8.24 x 14.1 x 2.40 mm
