d5aa962e/Transroc/Board/Transroc.sch

## KiCad design Board/Transroc.sch (2021-09-29)

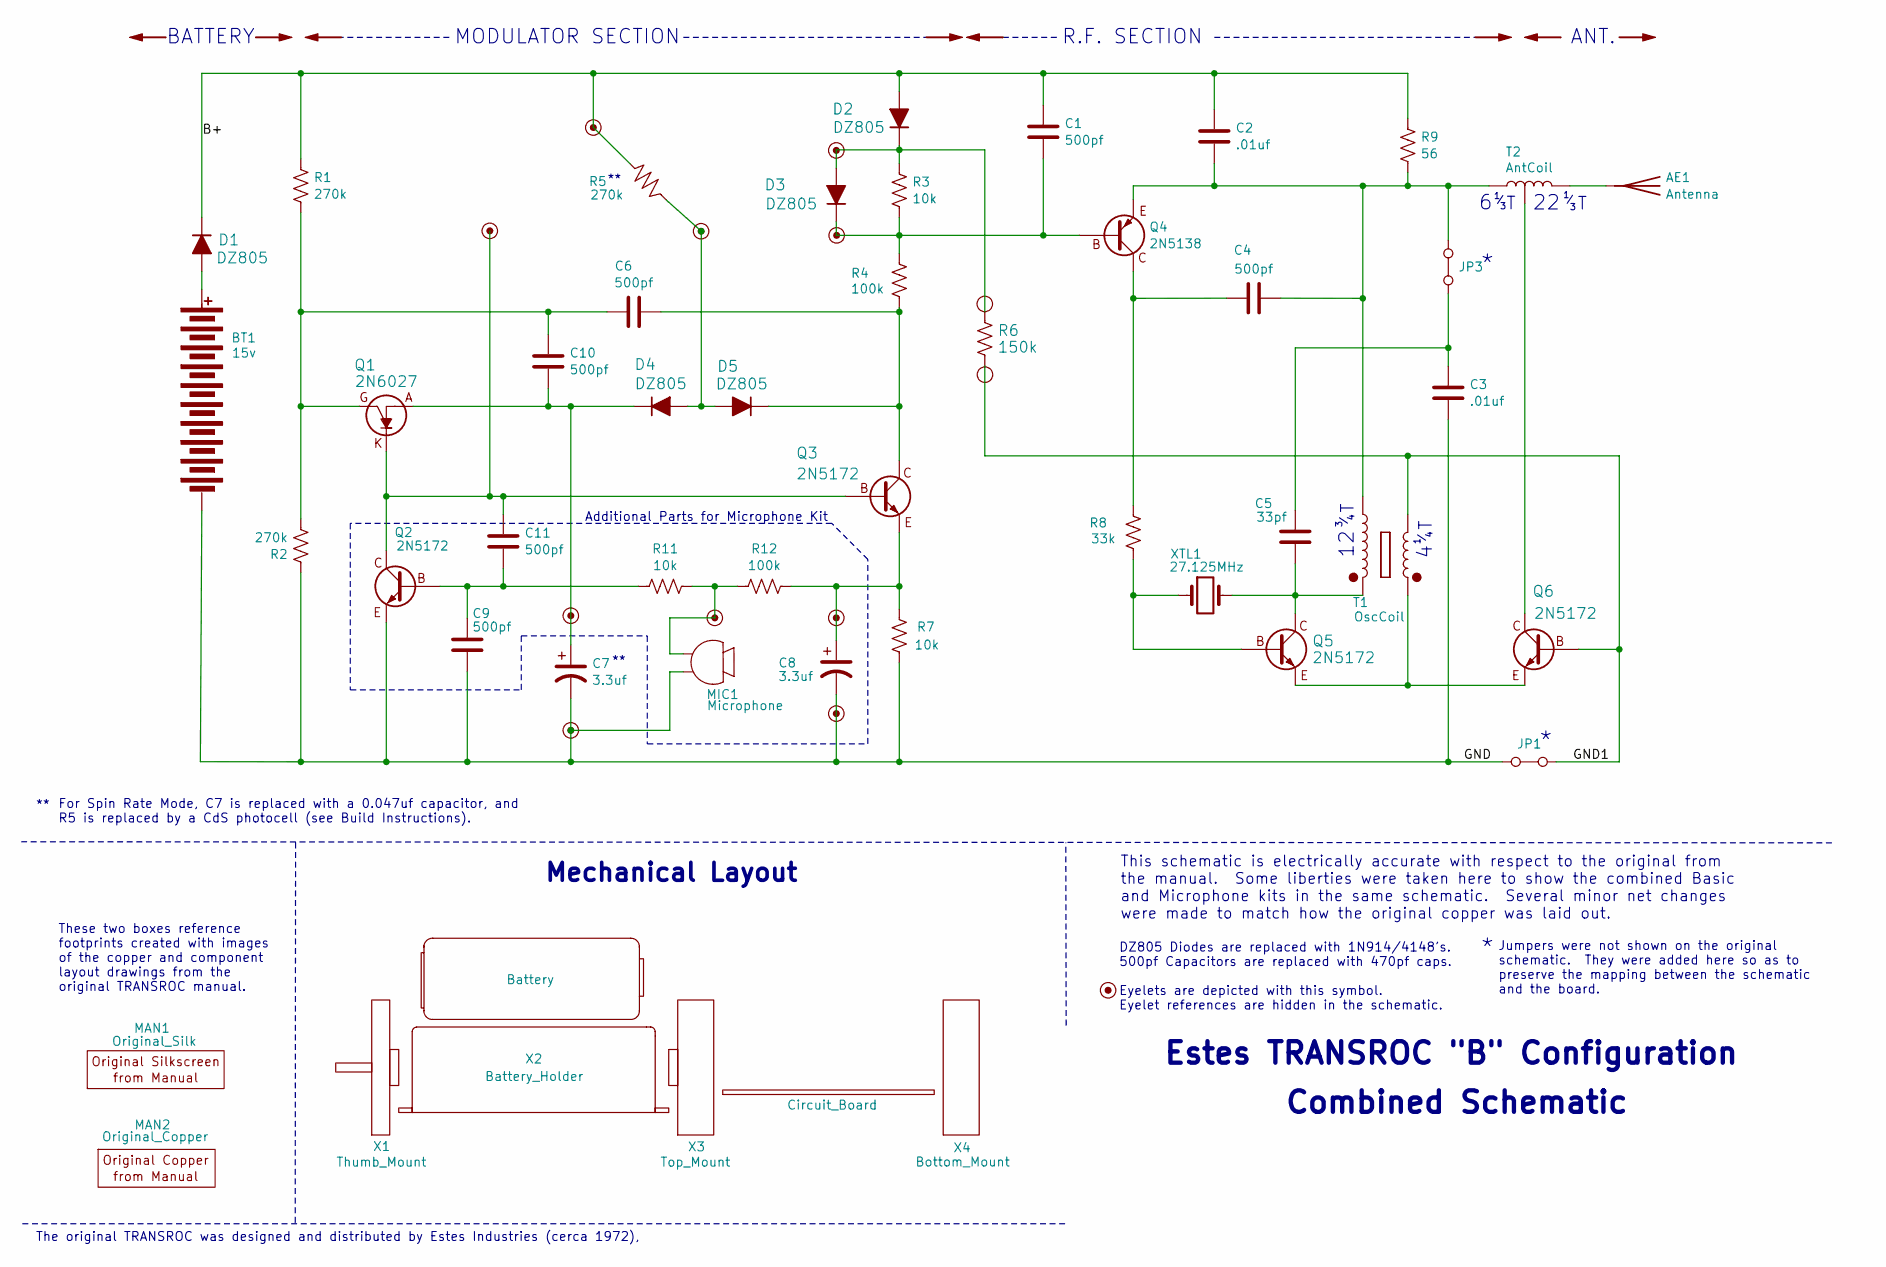
[picture p132: schematic Transroc.sch]

Parts:
AE1: Antenna
BT1: 15v; Battery
C1, C4, C6, C9, C10, C11: 500pf; Cap-7.5mm-v2
C2, C3: .01uf; Cap-4.5mm-v2
C5: 33pf; Cap-5.3mm-v2
C7: 3.3uf; ElecCap-4.72
C8: 3.3uf; ElectCap
D1, D3: DZ805; DZ805-CathodeUp
D2, D4, D5: DZ805; DZ805-AnodeUp
E1: Eyelet
JP1: Wire_Jumper; JP1
JP3: Wire_Jumper; JP2
MAN1: Original_Silk
MAN2: Original_Copper
MIC1: Microphone
Q1: 2N6027; TO-98
Q2, Q3, Q5, Q6: 2N5172; TO-98
Q4: 2N5138; TO-106
R1: 270k; Resistor-9.45mm
R2: 270k; Resistor-3.26mm
R3, R11: 10k; Resistor-2.83mm
R4: 100k; Resistor-3.95mm
R5: 270k; Resistor-5.77mm
R6: 150k; Resistor-10.83mm
R7: 10k; Resistor-4.53mm
R8: 33k; Resistor-4.53mm
R9: 56; Resistor-3.26mm
R12: 100k; Resistor-2.94mm
T1: OscCoil; Osc_Coil
T2: AntCoil; Ant_Coil
X1: Thumb_Mount; ThumbMount
X2: Battery_Holder; BatteryCompartment
X3: Top_Mount
X4: Bottom_Mount
XTL1: 27.125MHz; HC49_Crystal

Connections:
B+: C1.1, C2.1, D1.1 (K), D2.2 (A), R1.1, R5.1, R9.1
GND: BT1.2 (-), C3.2, C7.2, C8.2, C9.2, JP1.1 (1A), MIC1.2 (N), Q2.1 (E), R2.1, R7.1
GND1: JP1.2 (2A), Q6.2 (B), R6.2, T1.3 (Out1)
unnamed: AE1.1, T2.3 (Ant)
unnamed: BT1.1 (+), D1.2 (A)
unnamed: C1.2, D3.1 (K), Q4.2 (B), R3.2, R4.2
unnamed: C2.2, C4.1, JP3.1 (1A), Q4.1 (E), R9.2, T1.1 (In1), T2.1 (Base)
unnamed: C3.1, C5.1, JP3.2 (2A)
unnamed: C4.2, Q4.3 (C), R8.2
unnamed: C5.2, Q5.3 (C), T1.2 (In2), XTL1.2
unnamed: C6.1, D5.1 (K), Q3.3 (C), R4.1
unnamed: C8.1, Q3.1 (E), R7.2, R12.1
unnamed: C6.2, C10.1, Q1.3 (G), R1.2, R2.2
unnamed: C7.1, C10.2, D4.1 (K), Q1.1 (A)
unnamed: C11.1, Q1.2 (K), Q2.3 (C), Q3.2 (B)
unnamed: C9.1, C11.2, Q2.2 (B), R11.2
unnamed: D2.1 (K), D3.2 (A), R3.1, R6.1
unnamed: D4.2 (A), D5.2 (A), R5.2
unnamed: MIC1.1, R11.1, R12.2
unnamed: Q5.1 (E), Q6.1 (E), T1.4 (Out2)
unnamed: Q5.2 (B), R8.1, XTL1.1
unnamed: Q6.3 (C), T2.2 (Drive)

Notes on the sheet:
MODULATOR SECTION
R.F. SECTION
ANT.
BATTERY
Additional Parts for Microphone Kit
Estes TRANSROC "B" Configuration
Combined Schematic
Jumpers were not shown on the original schematic. They were added here so as to preserve the mapping between the schematic and the board.
Mechanical Layout
This schematic is electrically accurate with respect to the original from the manual. Some liberties were taken here to show the combined Basic and Microphone kits in the same schematic. Several minor net changes were made to match how the original copper was laid out.
The original TRANSROC was designed and distributed by Estes Industries (cerca 1972),
DZ805 Diodes are replaced with 1N914/4148's. 500pf Capacitors are replaced with 470pf caps. Eyelets are depicted with this symbol. Eyelet references are hidden in the schematic.
These two boxes reference footprints created with images of the copper and component layout drawings from the original TRANSROC manual.
For Spin Rate Mode, C7 is replaced with a 0.047uf capacitor, and R5 is replaced by a CdS photocell (see Build Instructions).
